Buski10/Offroad-CAD/Import/ToF Bilder/Bild1.jpg

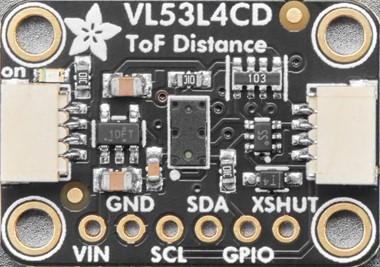
Import/ToF Bilder/Bild1.jpg
