Buski10/Offroad-CAD/Aufsamlung/Arm.SLDPRT

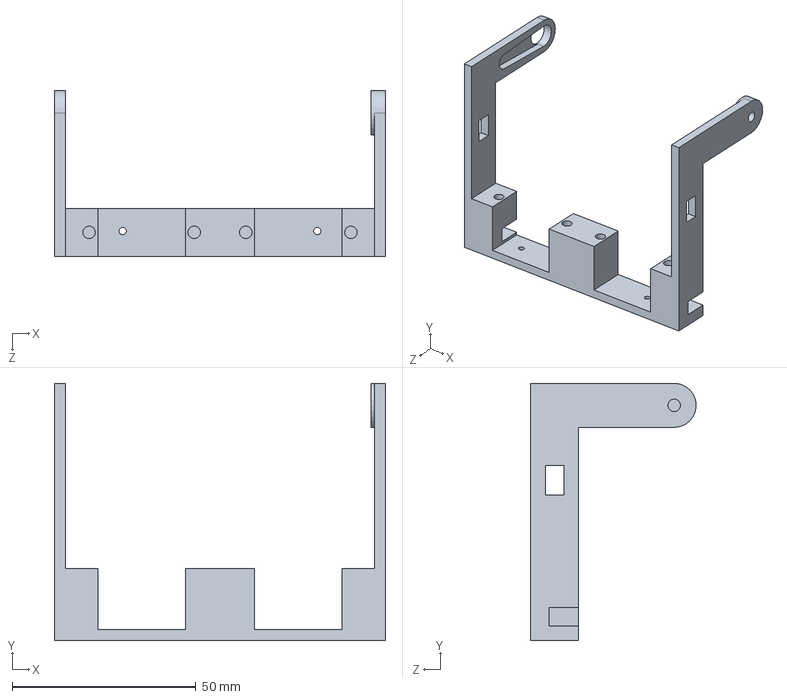
[picture p13: CAD file, 2025-10-28]
Aufsamlung/Arm.SLDPRT
90.0 x 70.0 x 45.0 mm
