Buski10/Offroad-CAD/Fahrgestell/Kamerabox.SLDPRT

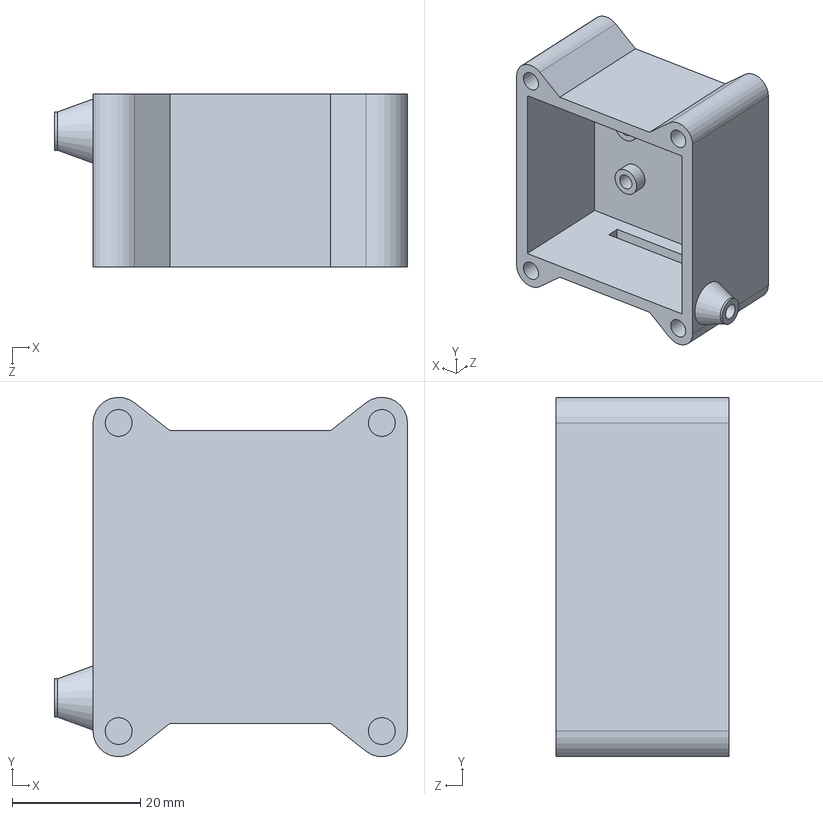
[picture p14: CAD file, 2025-10-28]
Fahrgestell/Kamerabox.SLDPRT
55.0 x 56.0 x 27.0 mm
