Buski10/Offroad-CAD/Import/BNO055/Adafruit_BNO055.SLDPRT

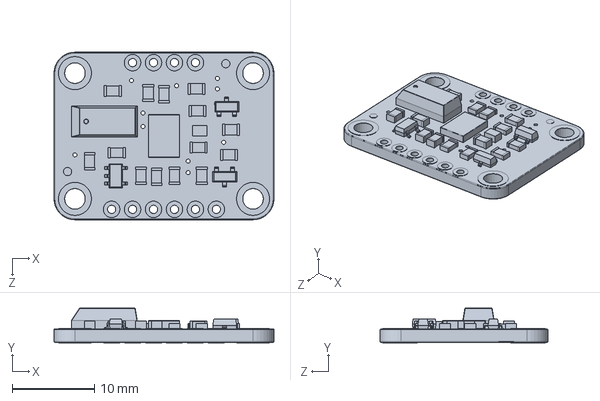
[picture p15: CAD file, 2025-10-28]
Import/BNO055/Adafruit_BNO055.SLDPRT
26.7 x 4.20 x 20.3 mm
