Buski10/Offroad-CAD/Import/ledRing/neopixel.SLDPRT

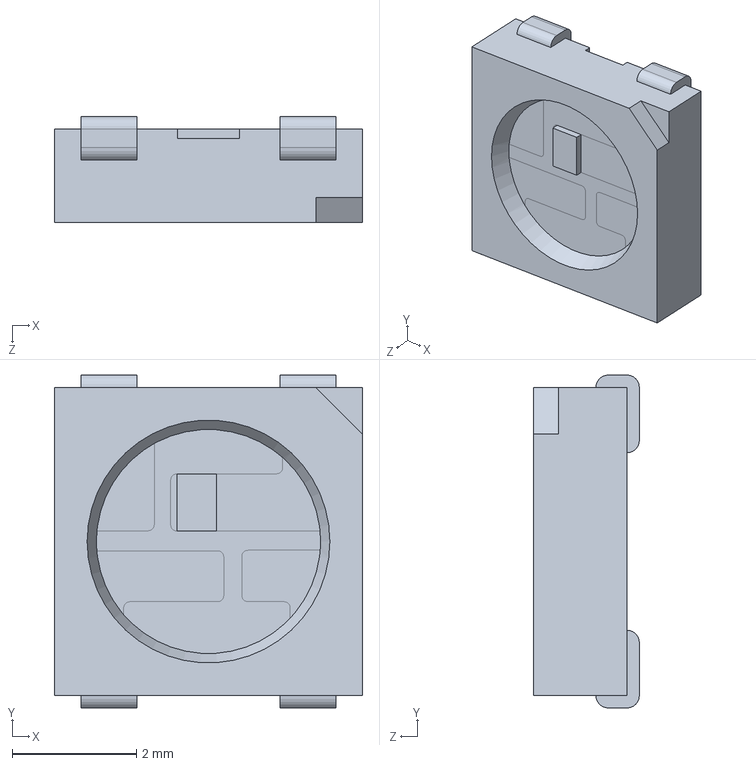
[picture p16: CAD file, 2025-10-28]
Import/ledRing/neopixel.SLDPRT
4.95 x 5.35 x 1.70 mm
