Buski10/Offroad-CAD/Import/Pin Header/pin-90deg.SLDPRT

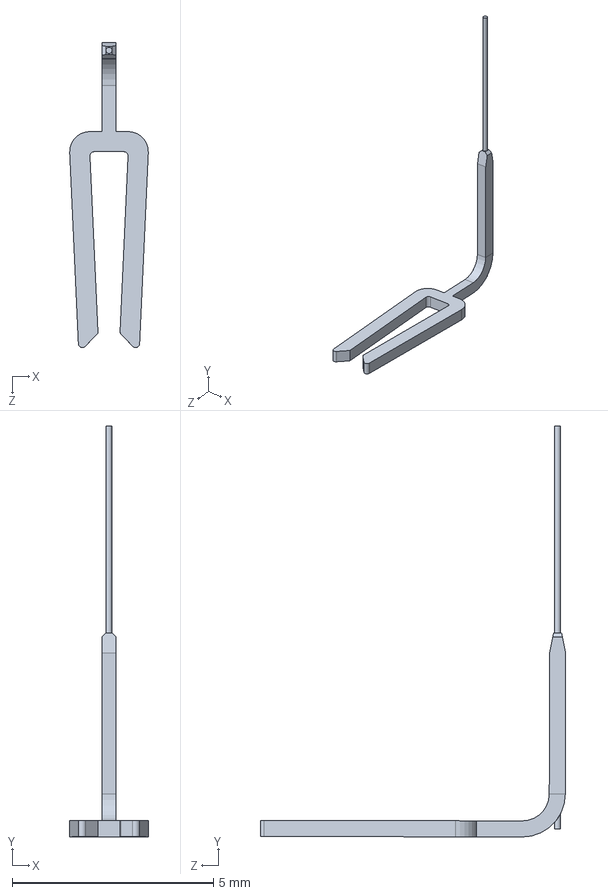
[picture p17: CAD file, 2025-10-28]
Import/Pin Header/pin-90deg.SLDPRT
1.95 x 10.2 x 7.58 mm
