Buski10/Offroad-CAD/Import/rpiCamera/kameraBlickwinkel.SLDPRT

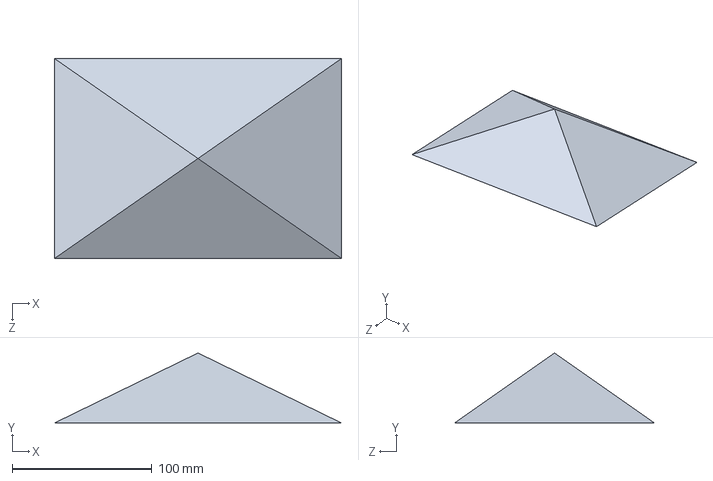
[picture p18: CAD file, 2025-10-28]
Import/rpiCamera/kameraBlickwinkel.SLDPRT
205.0 x 50.0 x 142.8 mm
