Buski10/Offroad-CAD/Import/Schwarz Kugel.SLDPRT

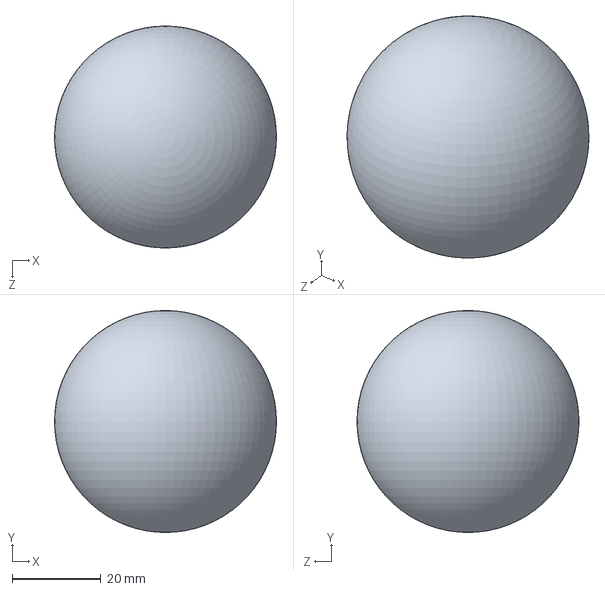
[picture p19: CAD file, 2025-10-28]
Import/Schwarz Kugel.SLDPRT
50.0 x 50.0 x 50.0 mm
