Buski10/Offroad-CAD/Import/Stepper Hat/terminal block_2.SLDPRT

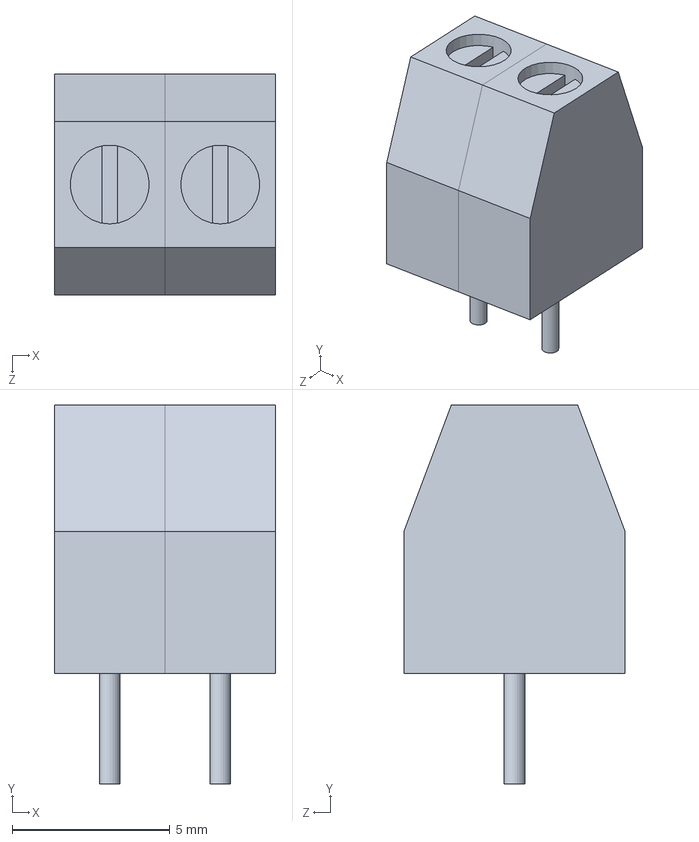
[picture p20: CAD file, 2025-10-28]
Import/Stepper Hat/terminal block_2.SLDPRT
7.00 x 12.0 x 7.00 mm
