Buski10/Offroad-CAD/Motorhalterungen/Achse Motorhalterung.SLDPRT

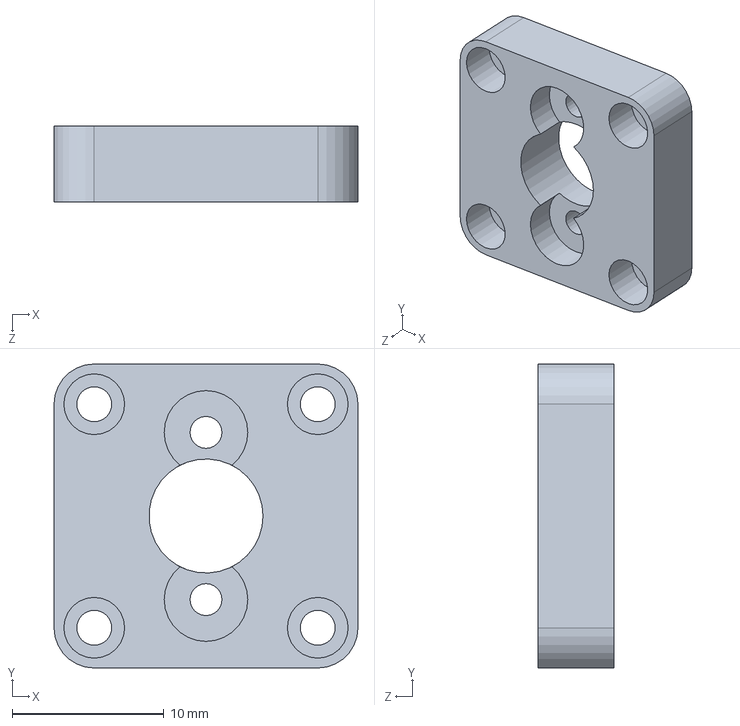
[picture p21: CAD file, 2025-10-28]
Motorhalterungen/Achse Motorhalterung.SLDPRT
20.0 x 20.0 x 5.00 mm
