Buski10/Offroad-CAD/Räder/Radschraube.SLDPRT

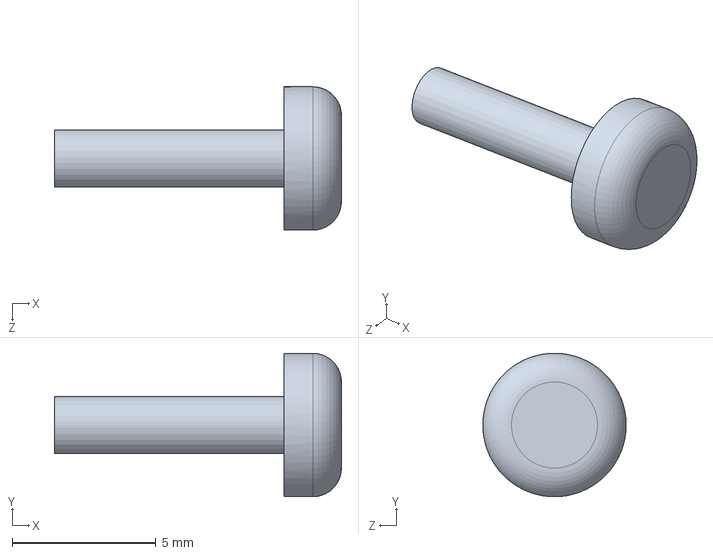
[picture p22: CAD file, 2025-10-28]
Räder/Radschraube.SLDPRT
10.0 x 5.00 x 5.00 mm
