Buski10/Offroad-CAD/Aufsamlung/Greifer.SLDPRT

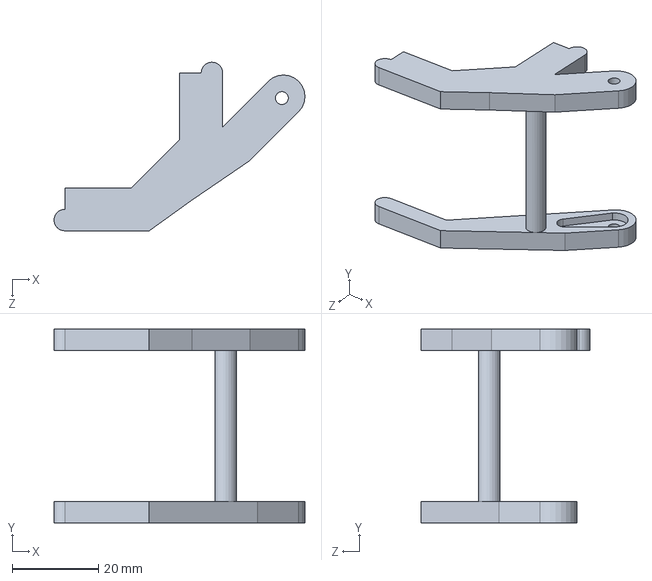
[picture p23: CAD file, 2025-10-28]
Aufsamlung/Greifer.SLDPRT
58.2 x 45.0 x 39.1 mm
