Buski10/Offroad-CAD/Fahrgestell/Grundplatte.SLDPRT

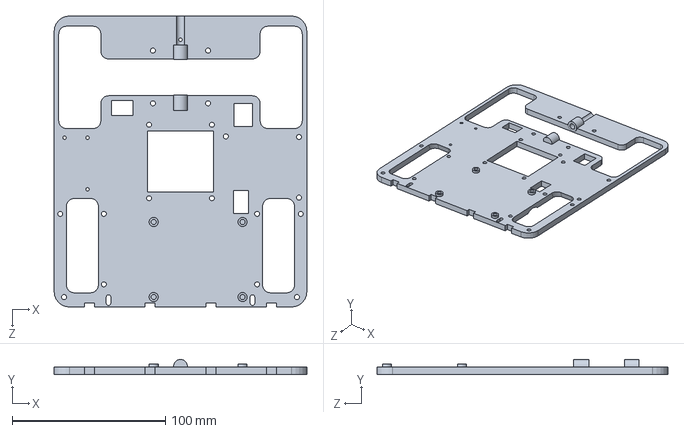
[picture p24: CAD file, 2025-10-28]
Fahrgestell/Grundplatte.SLDPRT
165.0 x 10.0 x 190.0 mm
