Buski10/Offroad-CAD/Import/ledRing/GRM188R60J226MEA0J.SLDPRT

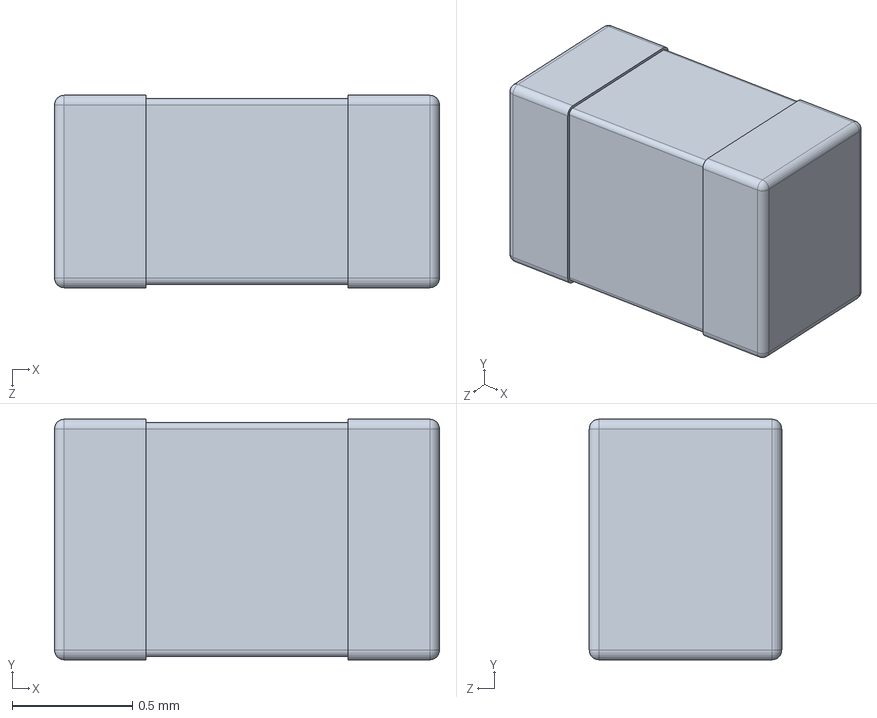
[picture p25: CAD file, 2025-10-28]
Import/ledRing/GRM188R60J226MEA0J.SLDPRT
1.60 x 1.00 x 0.8 mm
