Buski10/Offroad-CAD/Import/Micro SD Card.SLDPRT

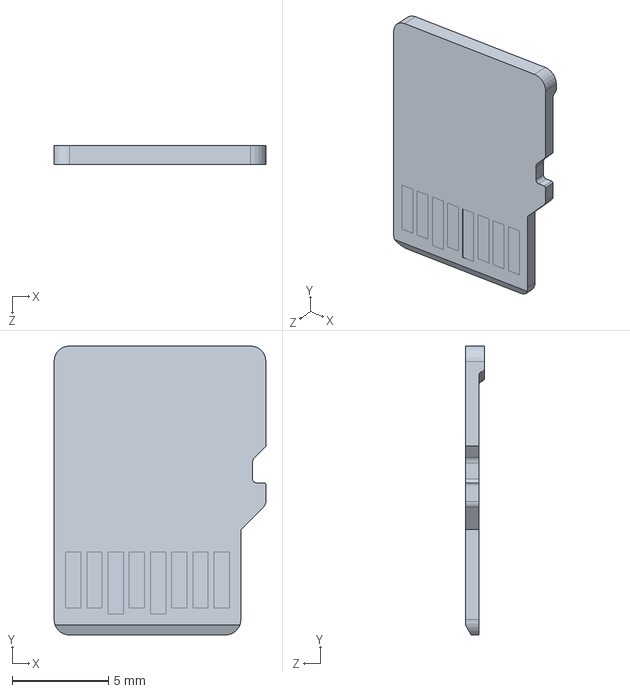
[picture p26: CAD file, 2025-10-28]
Import/Micro SD Card.SLDPRT
11.0 x 15.0 x 1.00 mm
