Buski10/Offroad-CAD/Import/Motor/1524T_SR.SLDPRT

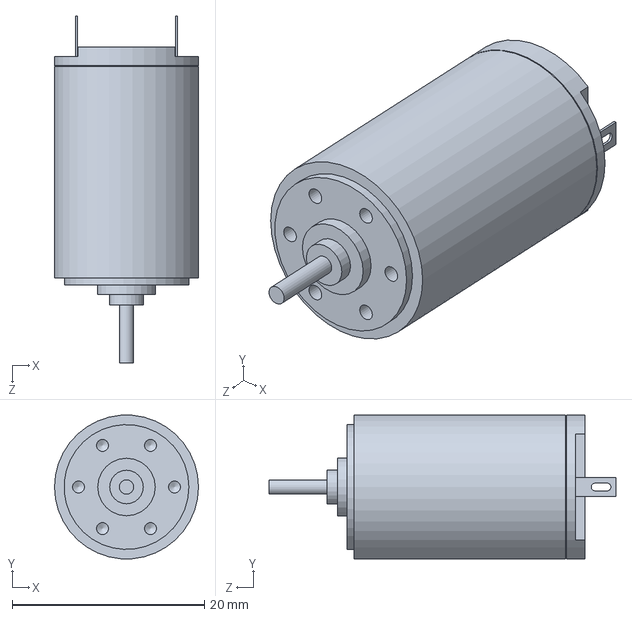
[picture p27: CAD file, 2025-10-28]
Import/Motor/1524T_SR.SLDPRT
15.0 x 14.9 x 36.1 mm
