Buski10/Offroad-CAD/Import/Pin Header/1x4 Male Pin Header Angle.SLDPRT

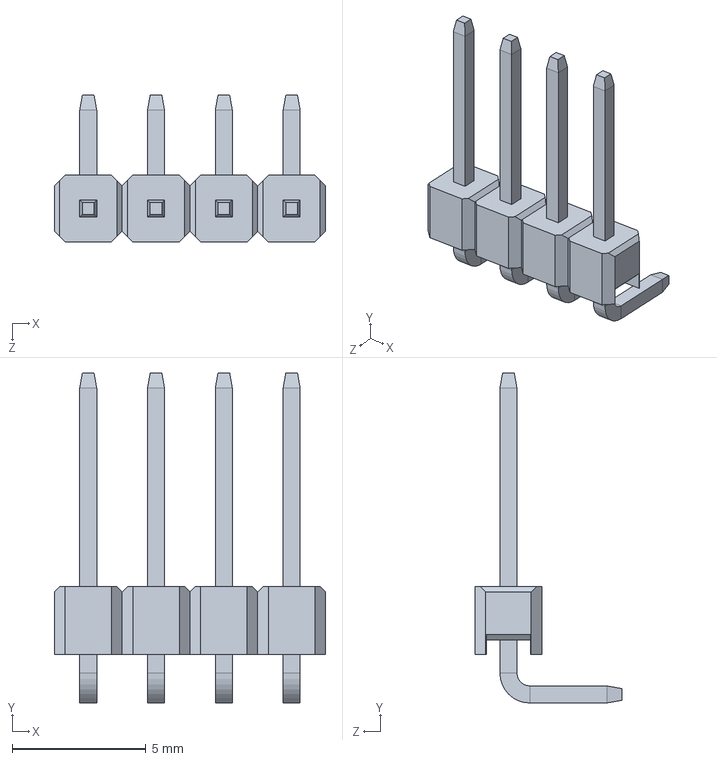
[picture p28: CAD file, 2025-10-28]
Import/Pin Header/1x4 Male Pin Header Angle.SLDPRT
10.2 x 12.4 x 5.50 mm
