Buski10/Offroad-CAD/Import/Stepper Hat/terminal block_3.SLDPRT

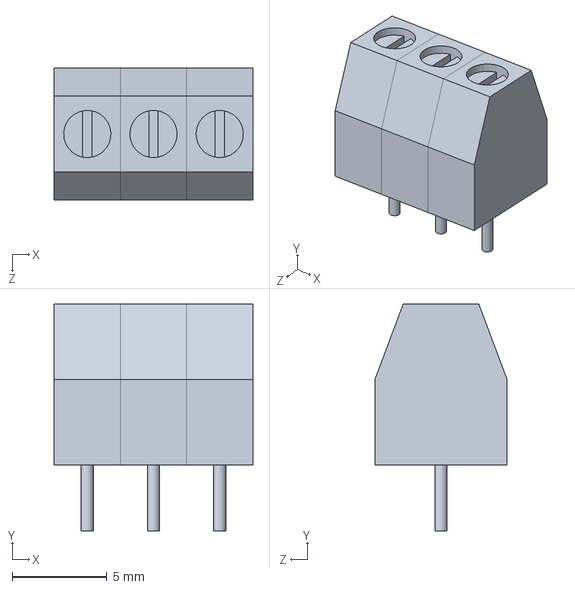
[picture p29: CAD file, 2025-10-28]
Import/Stepper Hat/terminal block_3.SLDPRT
10.5 x 12.0 x 7.00 mm
