Buski10/Offroad-CAD/Lipo Begrenzer.SLDPRT

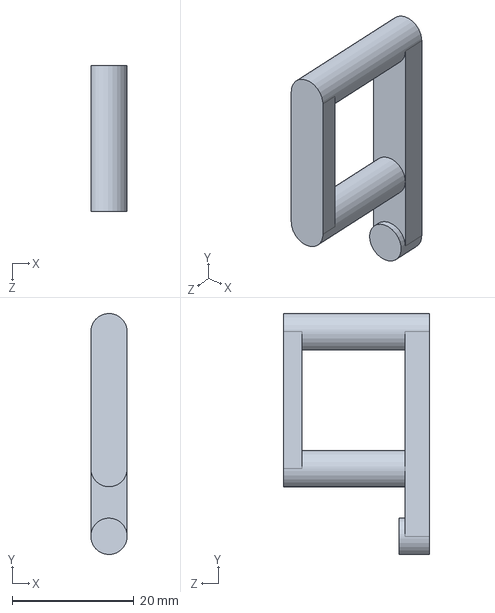
[picture p30: CAD file, 2025-10-28]
Lipo Begrenzer.SLDPRT
6.00 x 39.6 x 24.0 mm
