Buski10/Offroad-CAD/Motorhalterungen/Achse Motorhalterung rechts.SLDPRT

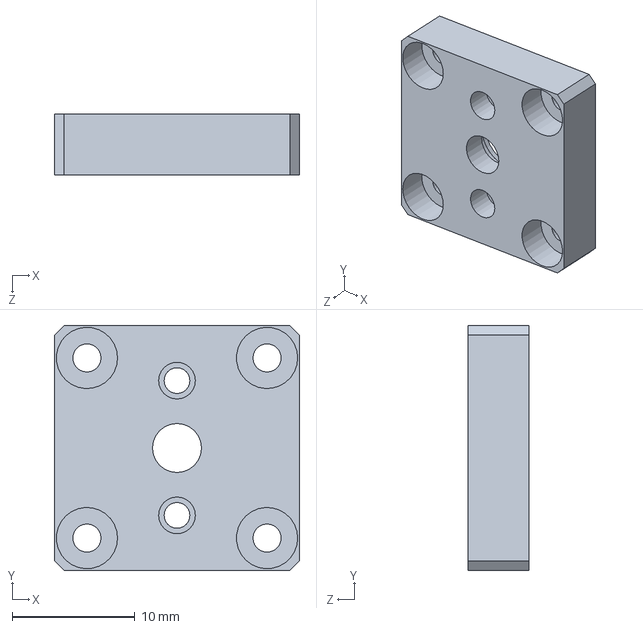
[picture p31: CAD file, 2025-10-28]
Motorhalterungen/Achse Motorhalterung rechts.SLDPRT
20.0 x 20.0 x 5.00 mm
