Buski10/Offroad-CAD/Rutsche/Kugelblocker.SLDPRT

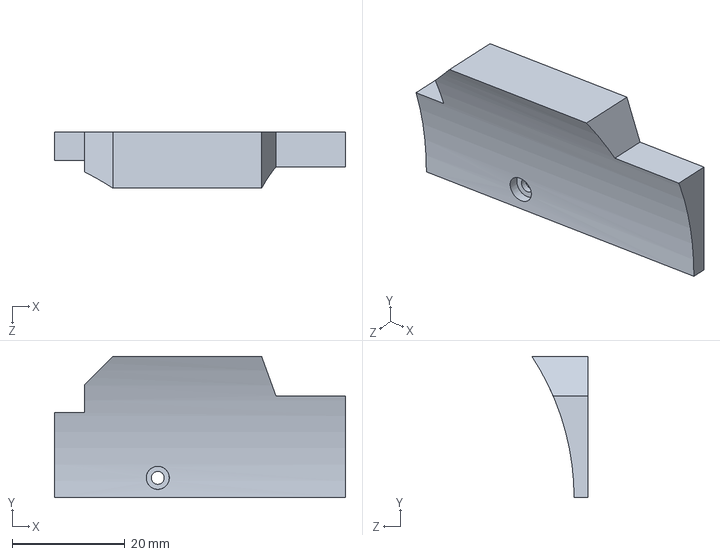
[picture p32: CAD file, 2025-10-28]
Rutsche/Kugelblocker.SLDPRT
51.7 x 25.1 x 10.0 mm
