Buski10/Offroad-CAD/Aufsamlung/SpiegelnGreifer.SLDPRT

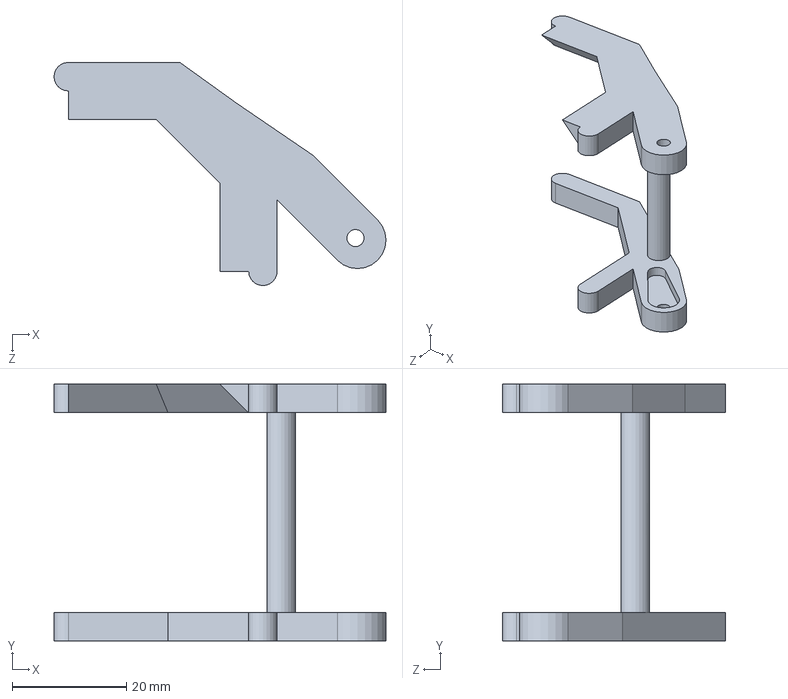
[picture p33: CAD file, 2025-10-28]
Aufsamlung/SpiegelnGreifer.SLDPRT
58.2 x 45.0 x 39.1 mm
