Buski10/Offroad-CAD/Import/7.5V, 3A step down.SLDPRT

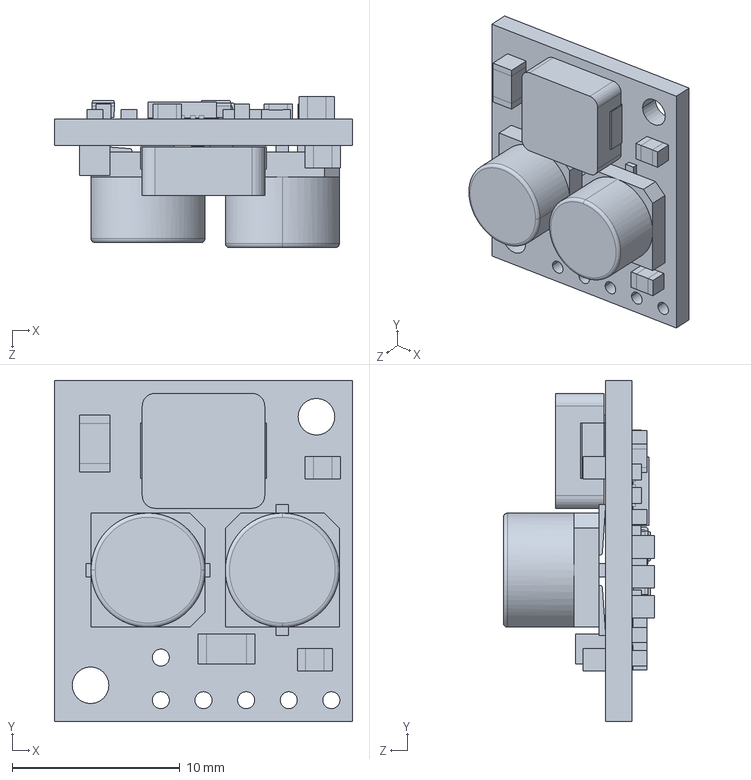
[picture p34: CAD file, 2025-10-28]
Import/7.5V, 3A step down.SLDPRT
17.8 x 20.3 x 9.02 mm
