Buski10/Offroad-CAD/Import/Motor/15A_3stage.SLDPRT

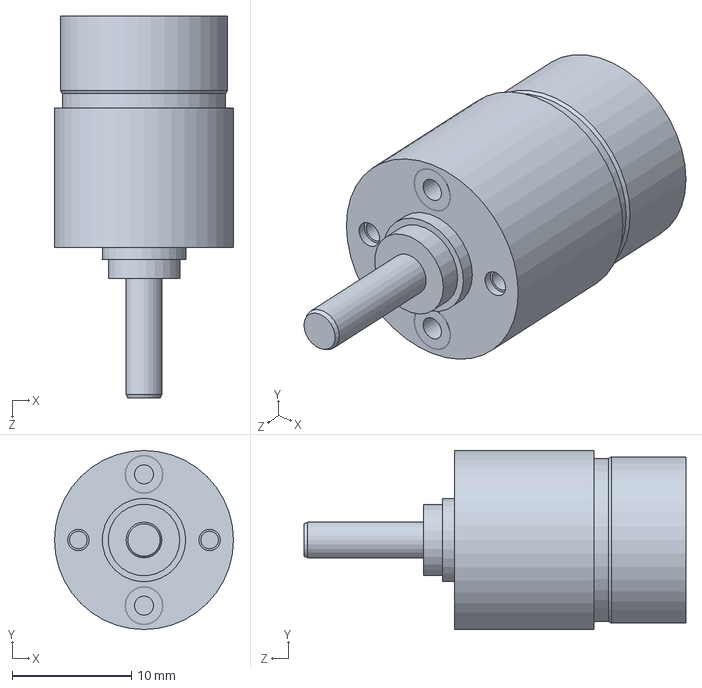
[picture p35: CAD file, 2025-10-28]
Import/Motor/15A_3stage.SLDPRT
15.0 x 15.0 x 32.0 mm
