Buski10/Offroad-CAD/Import/Pin Header/frame_H254.sldprt

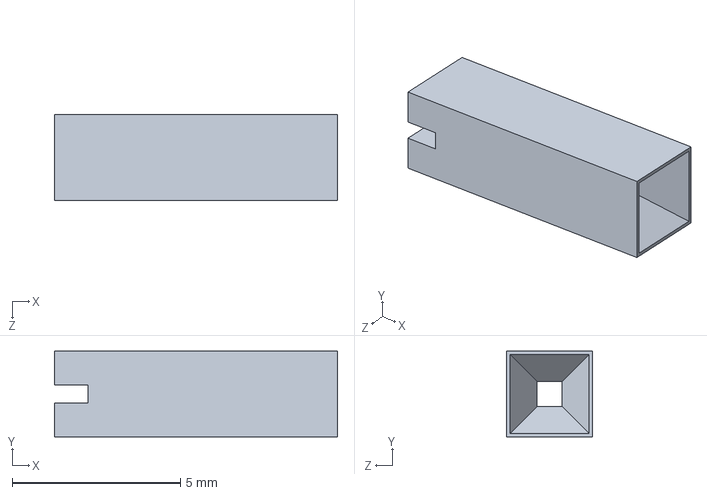
[picture p36: CAD file, 2025-10-28]
Import/Pin Header/frame_H254.sldprt
8.40 x 2.54 x 2.54 mm
