Buski10/Offroad-CAD/Import/RPi Active Cooler/Spring.SLDPRT

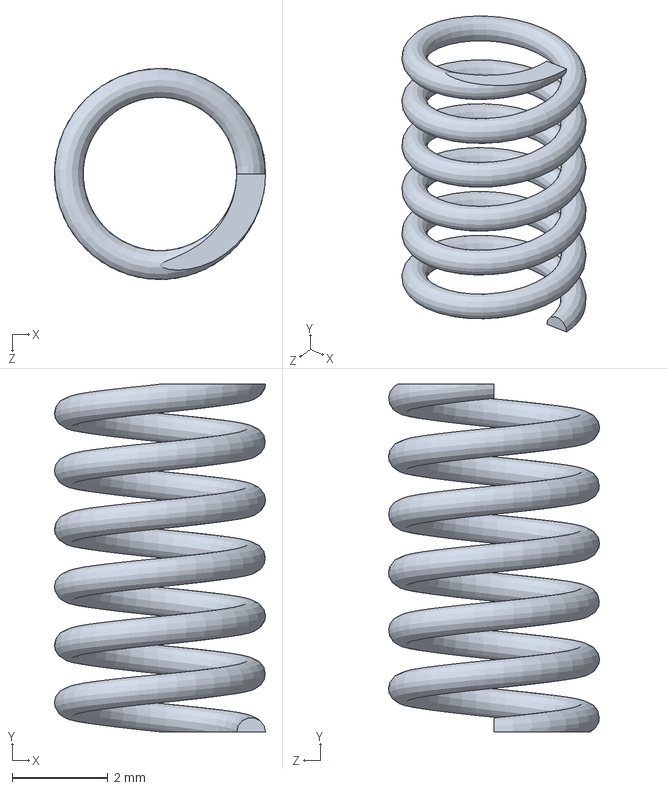
[picture p37: CAD file, 2025-10-28]
Import/RPi Active Cooler/Spring.SLDPRT
4.40 x 7.25 x 4.40 mm
