Buski10/Offroad-CAD/Import/rpiCamera/rpiCameraM.SLDPRT

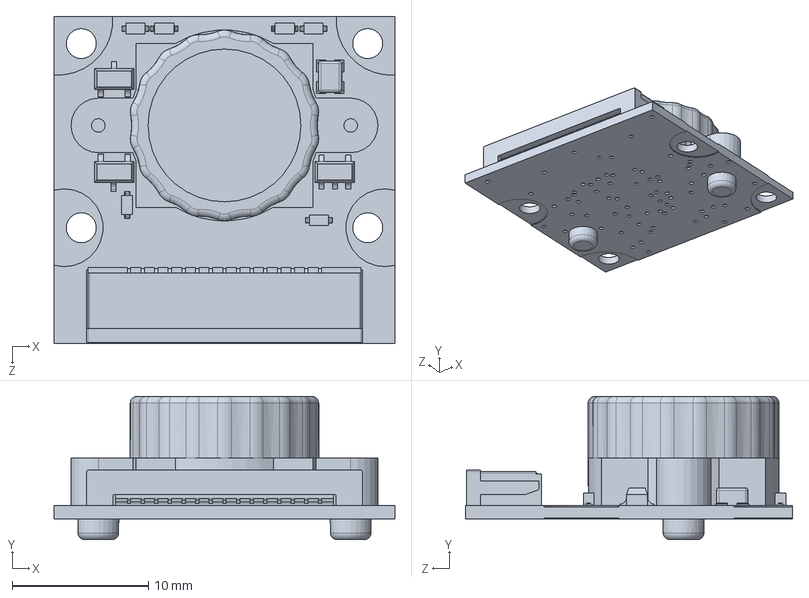
[picture p38: CAD file, 2025-10-28]
Import/rpiCamera/rpiCameraM.SLDPRT
25.0 x 10.5 x 24.0 mm
