Buski10/Offroad-CAD/Import/Stepper Hat/AdafruitStepperHat.SLDPRT

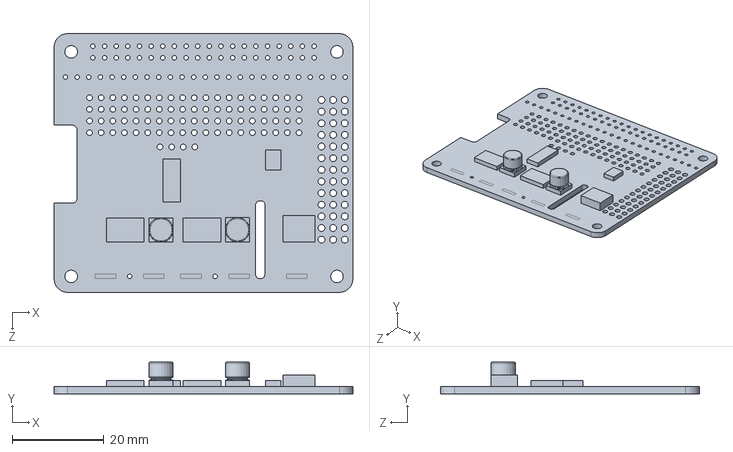
[picture p39: CAD file, 2025-10-28]
Import/Stepper Hat/AdafruitStepperHat.SLDPRT
65.2 x 6.90 x 56.5 mm
