Buski10/Offroad-CAD/Rutsche/Rutsche.SLDPRT

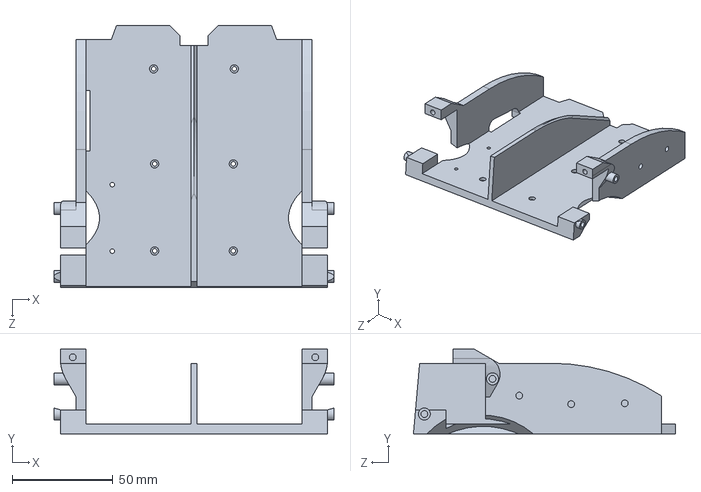
[picture p40: CAD file, 2025-10-28]
Rutsche/Rutsche.SLDPRT
138.9 x 42.0 x 130.0 mm
