Buski10/Offroad-CAD/Räder/Silikon Rad Guss.SLDPRT

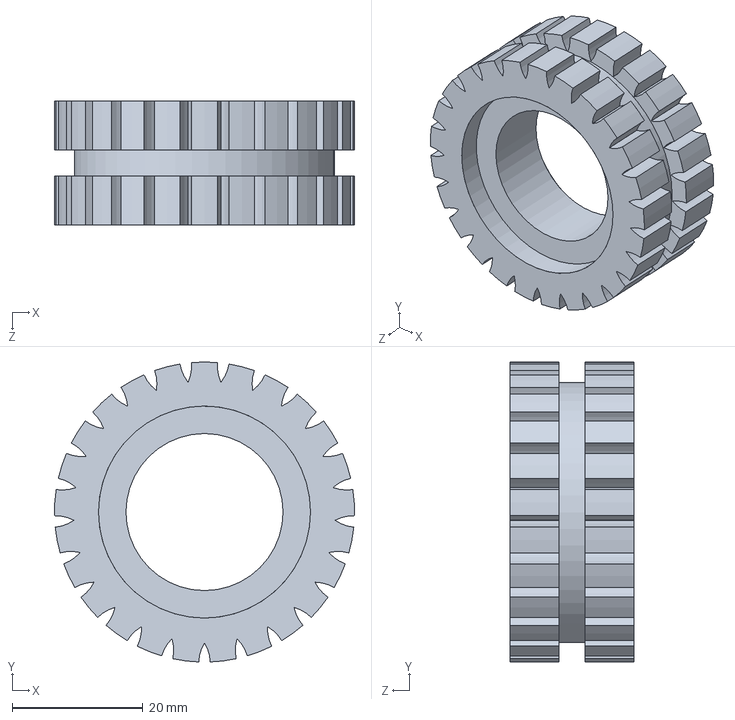
[picture p41: CAD file, 2025-10-28]
Räder/Silikon Rad Guss.SLDPRT
45.8 x 45.8 x 19.0 mm
