Buski10/Offroad-CAD/Tasterstange.SLDPRT

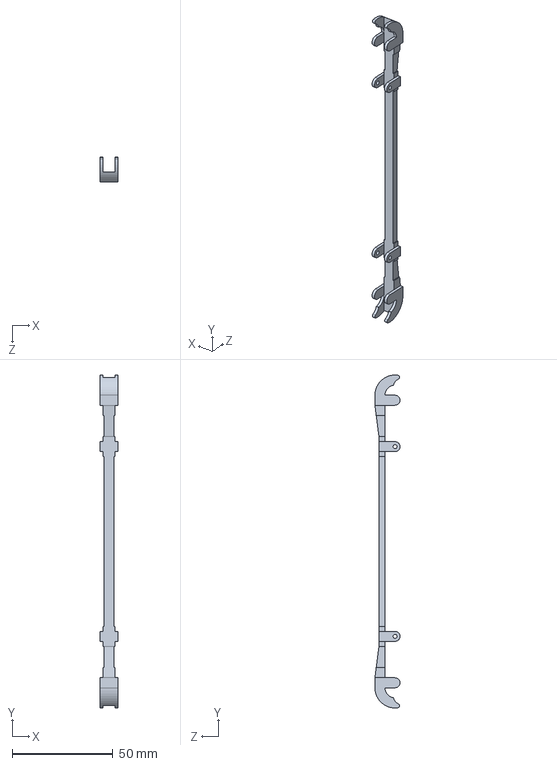
[picture p42: CAD file, 2025-10-28]
Tasterstange.SLDPRT
9.00 x 165.0 x 12.5 mm
