Buski10/Offroad-CAD/Import/Motor/15A_flange_a.stp.SLDPRT

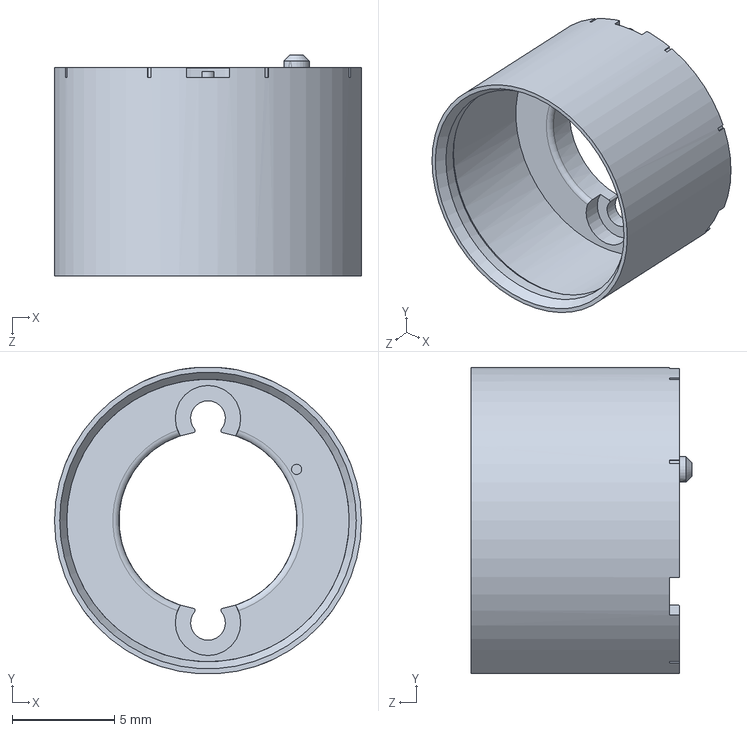
[picture p43: CAD file, 2025-10-28]
Import/Motor/15A_flange_a.stp.SLDPRT
15.0 x 15.0 x 10.8 mm
