Buski10/Offroad-CAD/Import/RPi Active Cooler/RotorBlades.SLDPRT

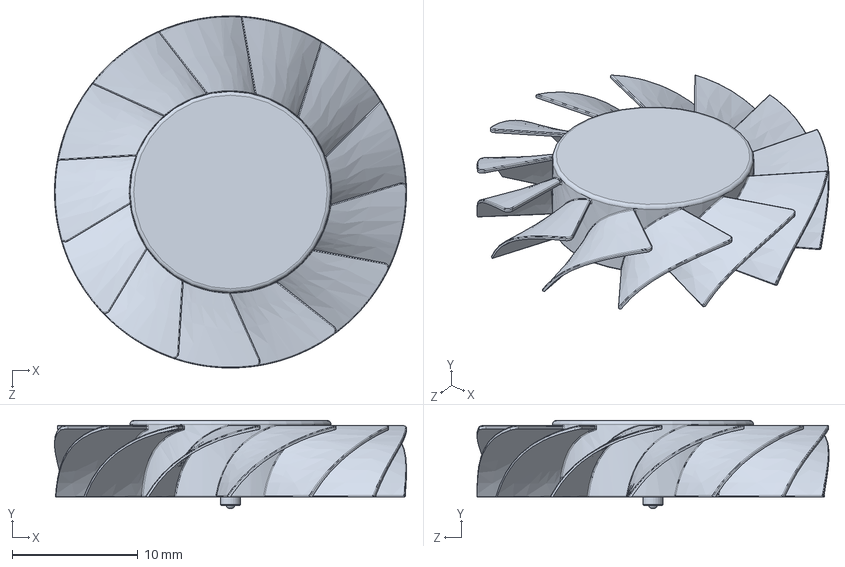
[picture p44: CAD file, 2025-10-28]
Import/RPi Active Cooler/RotorBlades.SLDPRT
28.0 x 7.00 x 28.0 mm
