Buski10/Offroad-CAD/Import/rpiCamera/rpiCameraM_lens.SLDPRT

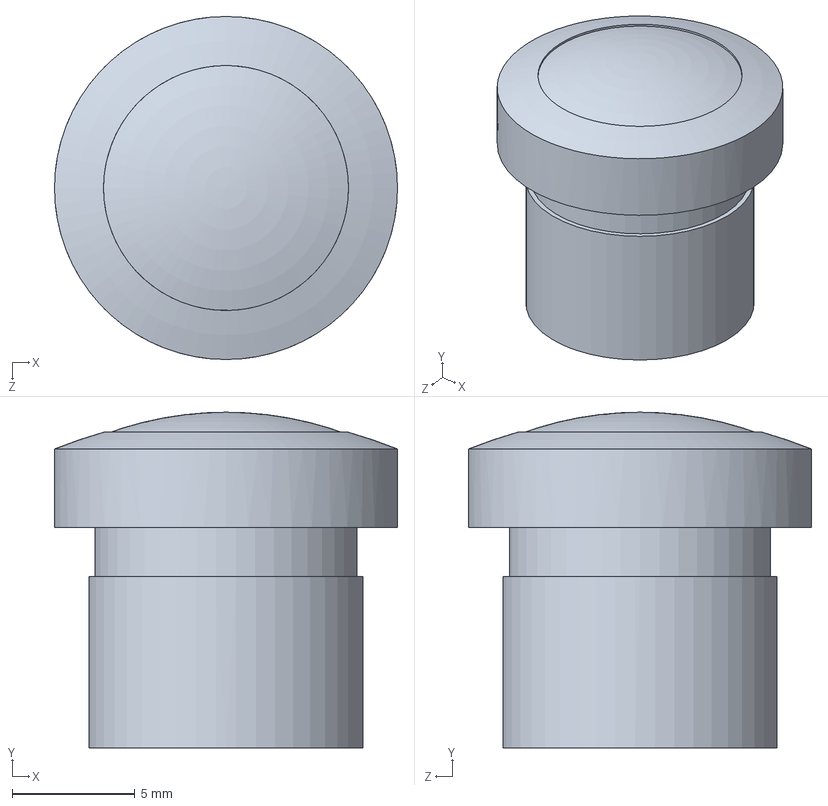
[picture p45: CAD file, 2025-10-28]
Import/rpiCamera/rpiCameraM_lens.SLDPRT
14.0 x 13.7 x 14.0 mm
