Buski10/Offroad-CAD/Import/Servo S90/MicroServo-SG90.SLDPRT

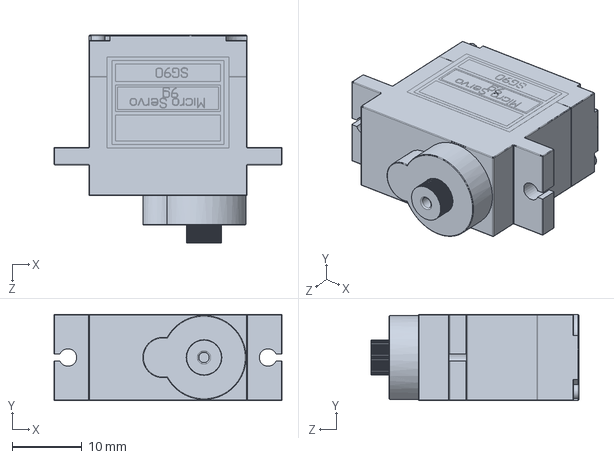
[picture p46: CAD file, 2025-10-28]
Import/Servo S90/MicroServo-SG90.SLDPRT
32.6 x 12.4 x 29.8 mm
