Buski10/Offroad-CAD/Import/Stepper Hat/40pin.SLDPRT

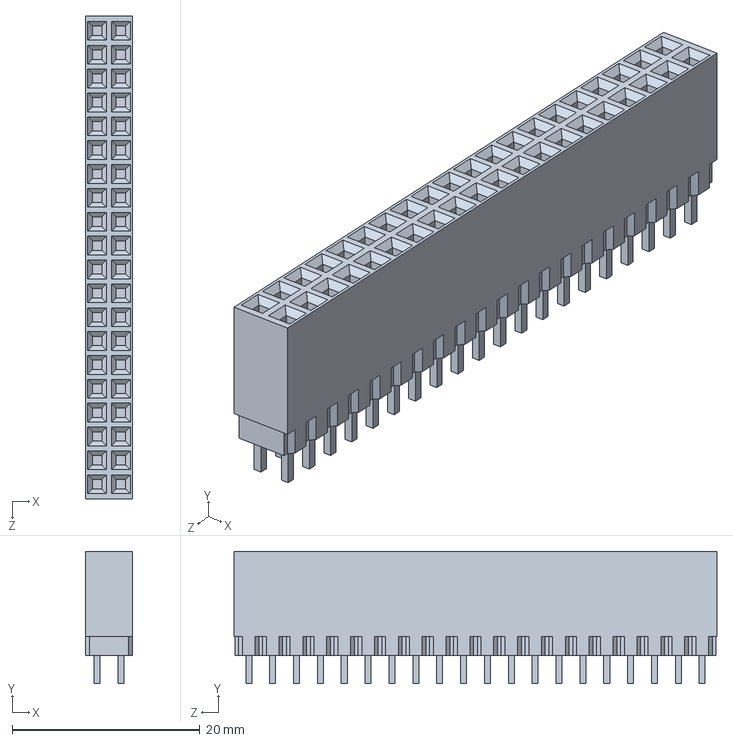
[picture p47: CAD file, 2025-10-28]
Import/Stepper Hat/40pin.SLDPRT
5.00 x 14.1 x 51.4 mm
