Buski10/Offroad-CAD/Import/usb-c-connector-board.SLDPRT

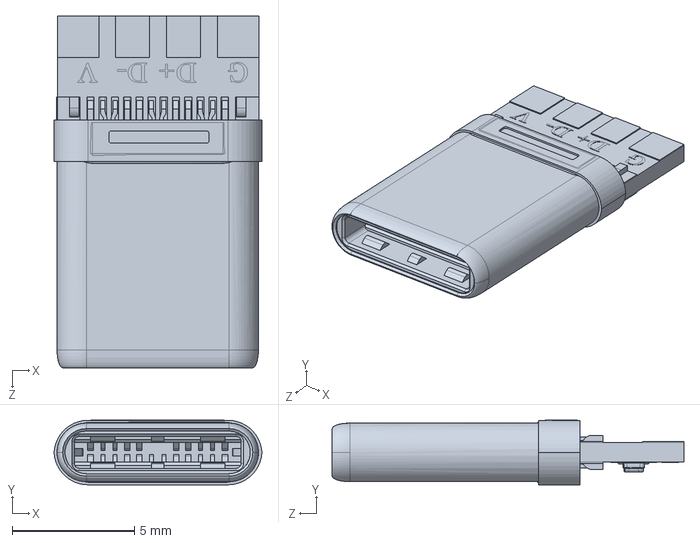
[picture p48: CAD file, 2025-10-28]
Import/usb-c-connector-board.SLDPRT
8.52 x 2.65 x 14.4 mm
