Buski10/Offroad-CAD/Rutsche/Schranke.SLDPRT

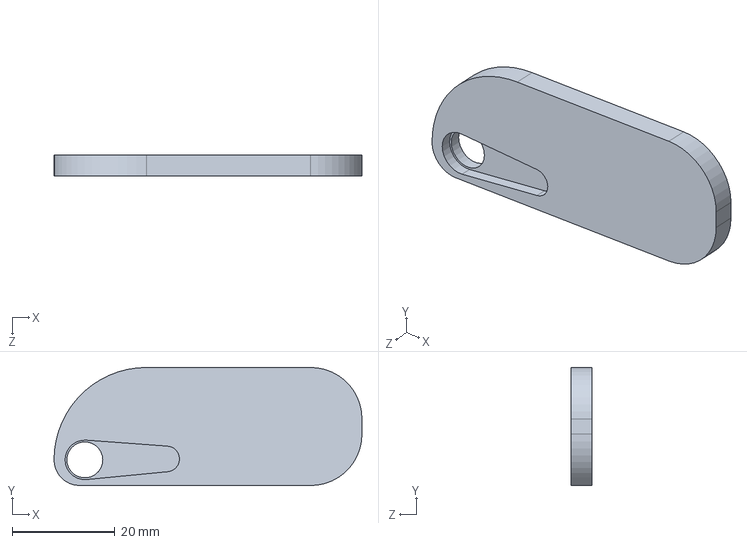
[picture p49: CAD file, 2025-10-28]
Rutsche/Schranke.SLDPRT
60.0 x 23.0 x 4.00 mm
