Buski10/Offroad-CAD/Räder/Silikon Rad.SLDPRT

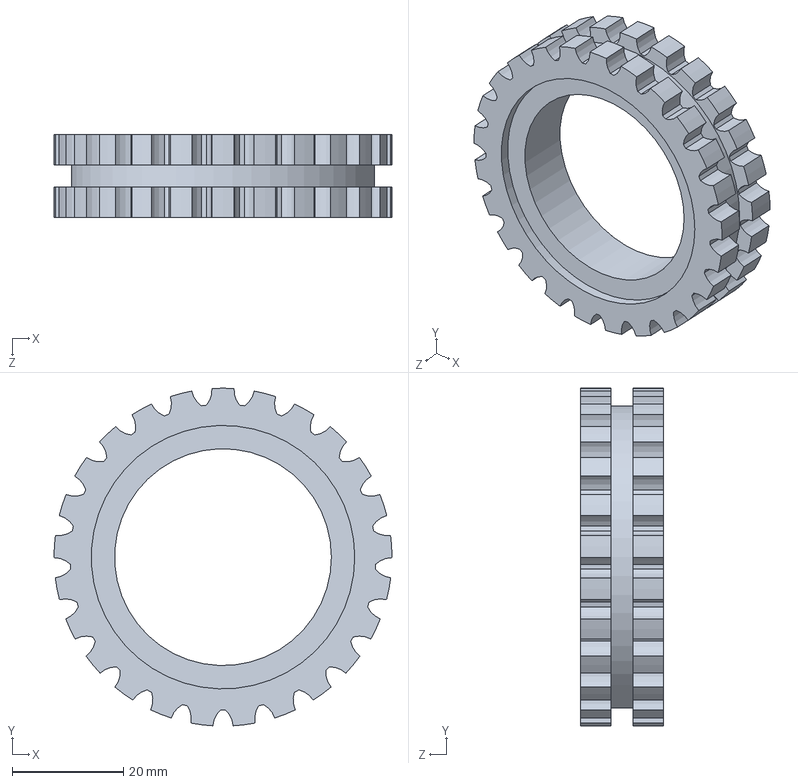
[picture p50: CAD file, 2025-10-28]
Räder/Silikon Rad.SLDPRT
60.8 x 60.7 x 15.0 mm
