Buski10/Offroad-CAD/ToF Vorne Links V2.0.SLDPRT

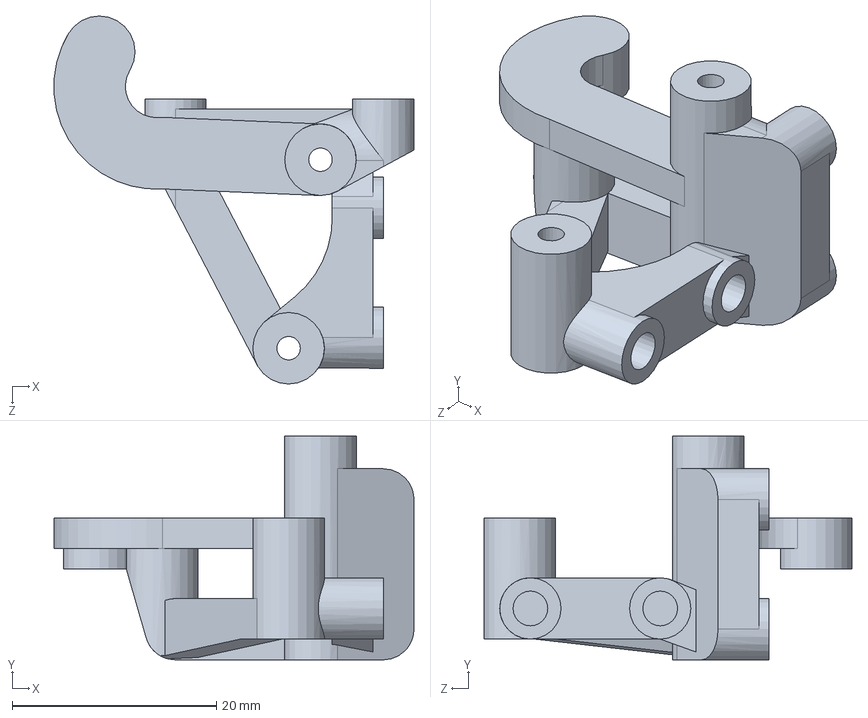
[picture p51: CAD file, 2025-10-28]
ToF Vorne Links V2.0.SLDPRT
35.2 x 21.9 x 36.0 mm
