Buski10/Offroad-CAD/Rutsche/Rutschehalterung.SLDPRT

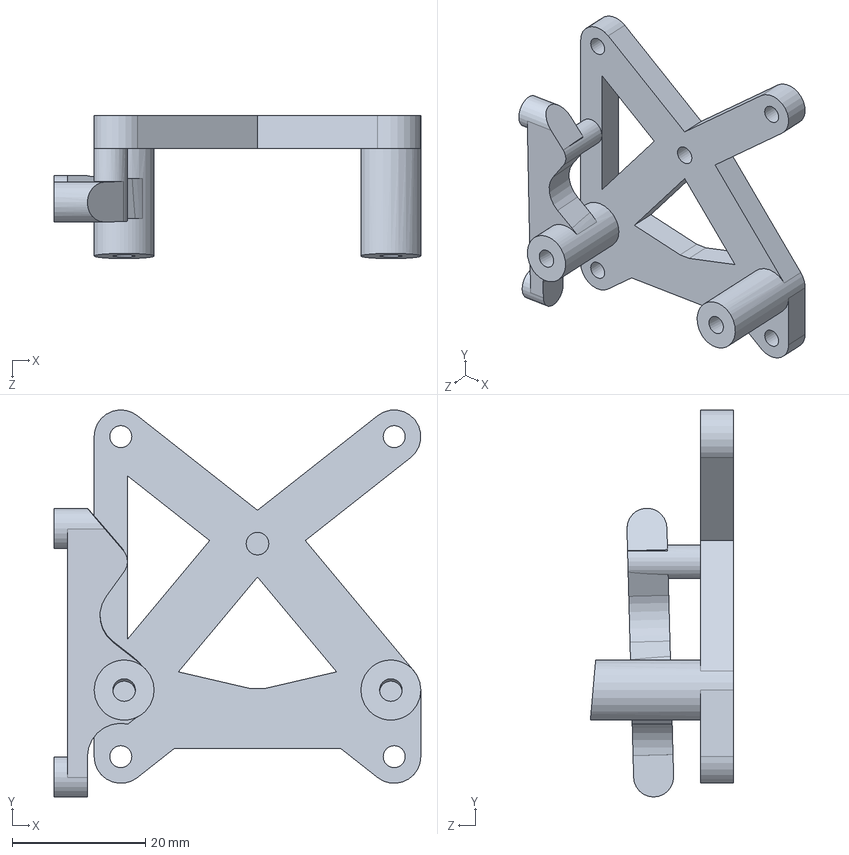
[picture p52: CAD file, 2025-10-28]
Rutsche/Rutschehalterung.SLDPRT
55.0 x 58.0 x 21.5 mm
