Buski10/Offroad-CAD/Räder/Felge.SLDPRT

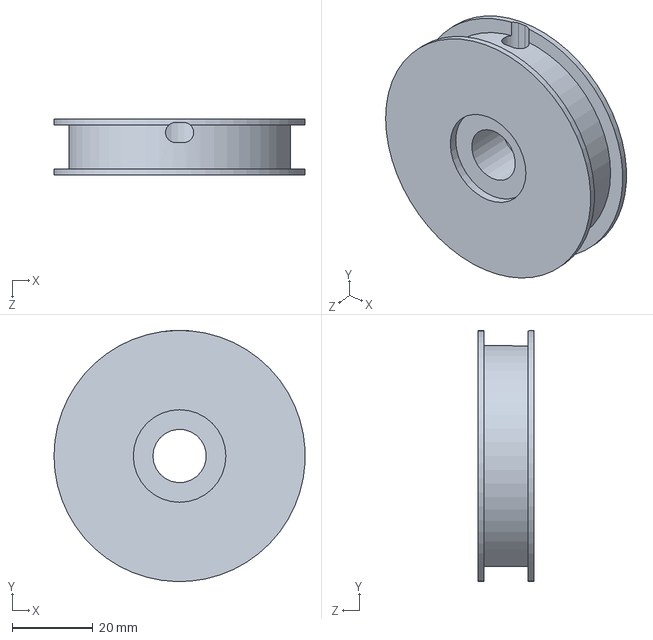
[picture p53: CAD file, 2025-10-28]
Räder/Felge.SLDPRT
62.3 x 62.4 x 14.0 mm
