Buski10/Offroad-CAD/Vordere Kamerahalterung.SLDPRT

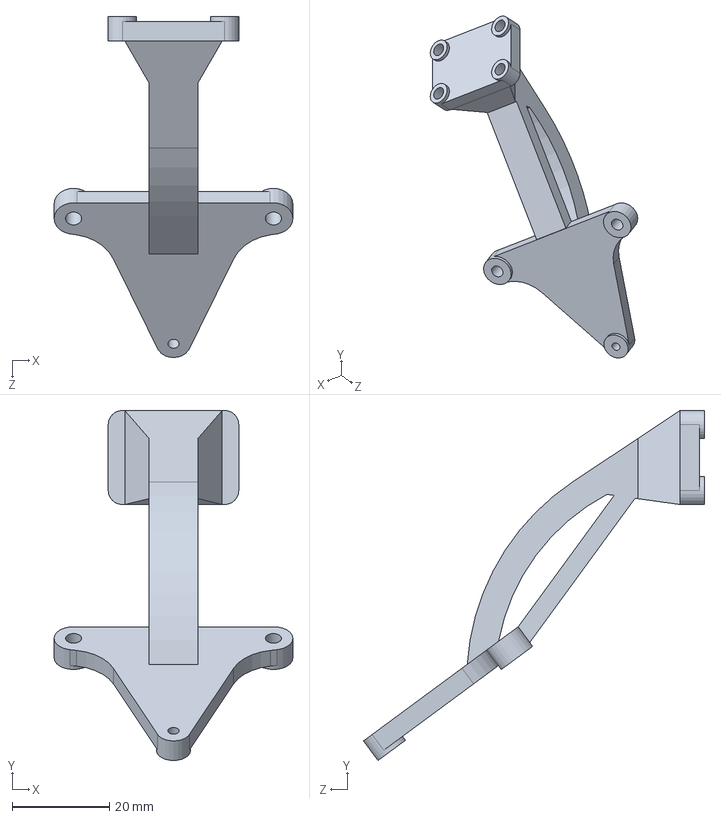
[picture p54: CAD file, 2025-10-28]
Vordere Kamerahalterung.SLDPRT
49.0 x 71.8 x 70.0 mm
