Buski10/Offroad-CAD/Import/RPi Active Cooler/Heatsink-fan-base_RPi5.SLDPRT

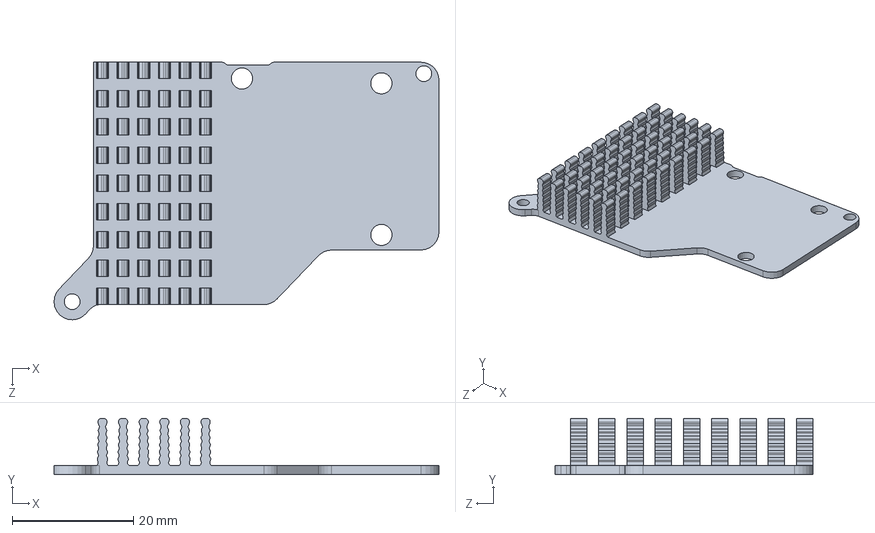
[picture p55: CAD file, 2025-10-28]
Import/RPi Active Cooler/Heatsink-fan-base_RPi5.SLDPRT
63.5 x 9.30 x 42.5 mm
