Buski10/Offroad-CAD/Kompliziertes Teil.SLDPRT

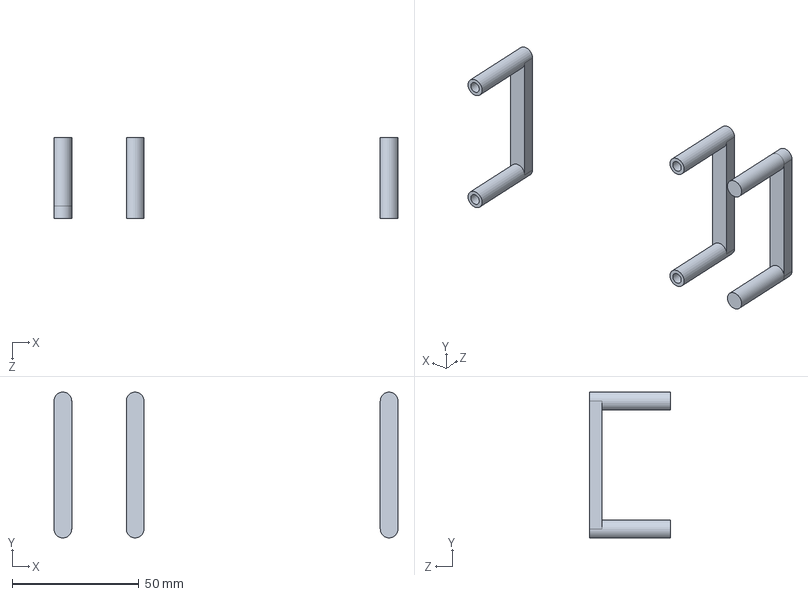
[picture p56: CAD file, 2025-10-28]
Kompliziertes Teil.SLDPRT
135.6 x 57.5 x 32.0 mm
