Buski10/Offroad-CAD/Motorhalterungen/Motorhalterung vorne.SLDPRT

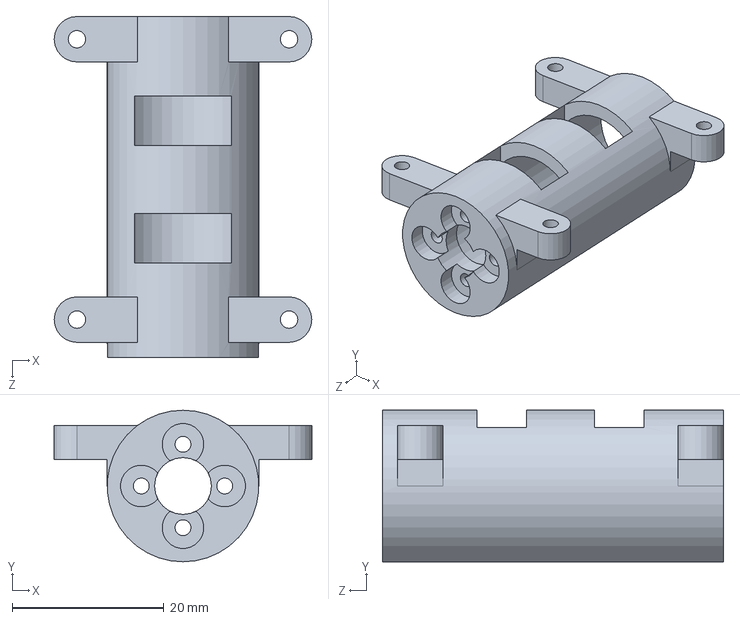
[picture p57: CAD file, 2025-10-28]
Motorhalterungen/Motorhalterung vorne.SLDPRT
34.0 x 20.0 x 45.0 mm
