Buski10/Offroad-CAD/Hintere ToF Halterung.SLDPRT

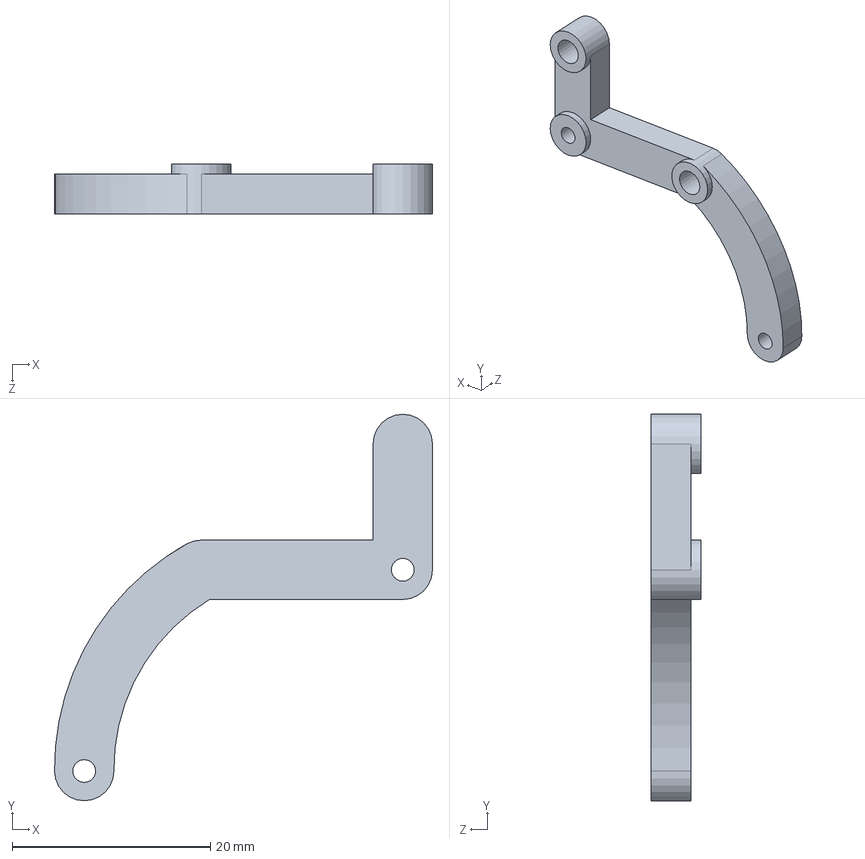
[picture p58: CAD file, 2025-10-28]
Hintere ToF Halterung.SLDPRT
38.2 x 39.0 x 5.00 mm
