Buski10/Offroad-CAD/Import/RPi Active Cooler/MotorHouse.SLDPRT

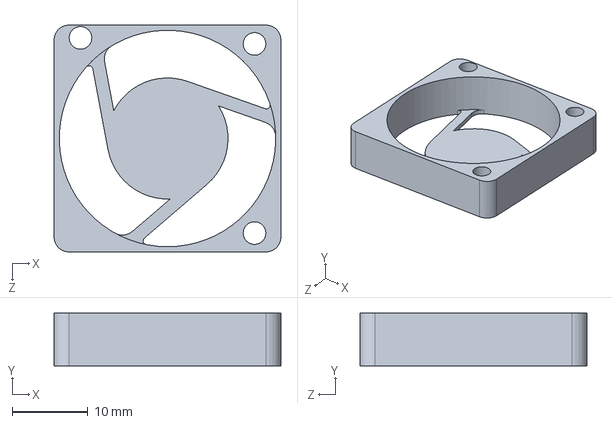
[picture p59: CAD file, 2025-10-28]
Import/RPi Active Cooler/MotorHouse.SLDPRT
30.0 x 7.00 x 30.0 mm
