Buski10/Offroad-CAD/Räder/Felgen Adapter.SLDPRT

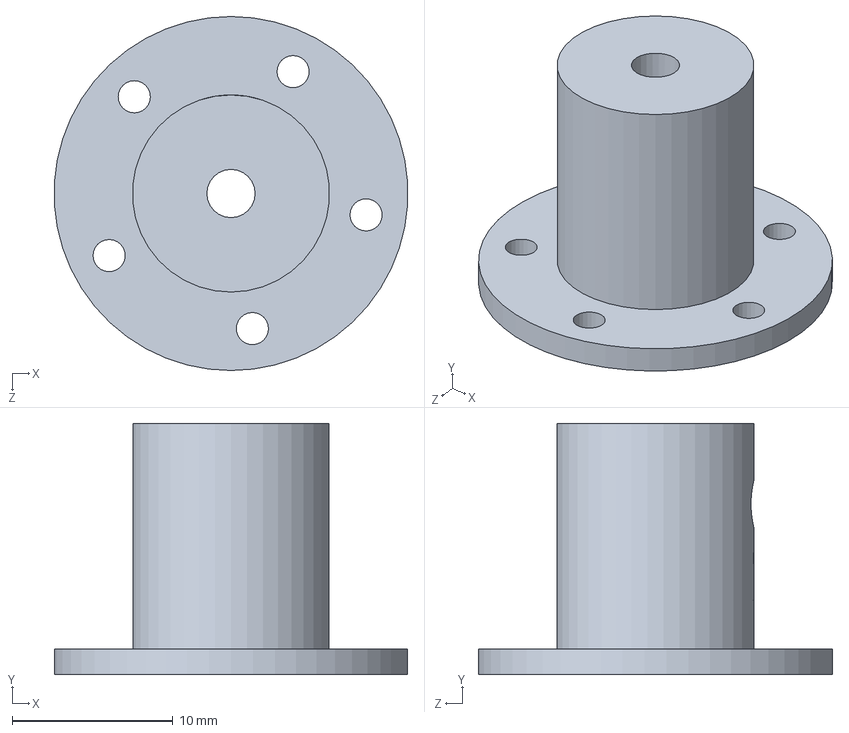
[picture p60: CAD file, 2025-10-28]
Räder/Felgen Adapter.SLDPRT
22.0 x 15.6 x 22.0 mm
