Buski10/Offroad-CAD/Greifer Servo Halterung.SLDPRT

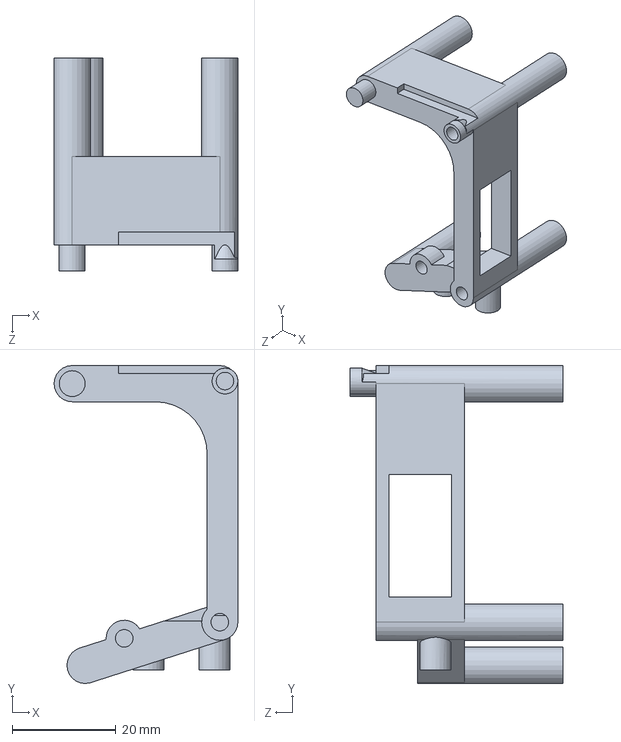
[picture p61: CAD file, 2025-10-28]
Greifer Servo Halterung.SLDPRT
35.5 x 61.4 x 41.0 mm
