Buski10/Offroad-CAD/Import/KST_DS215MG.SLDPRT

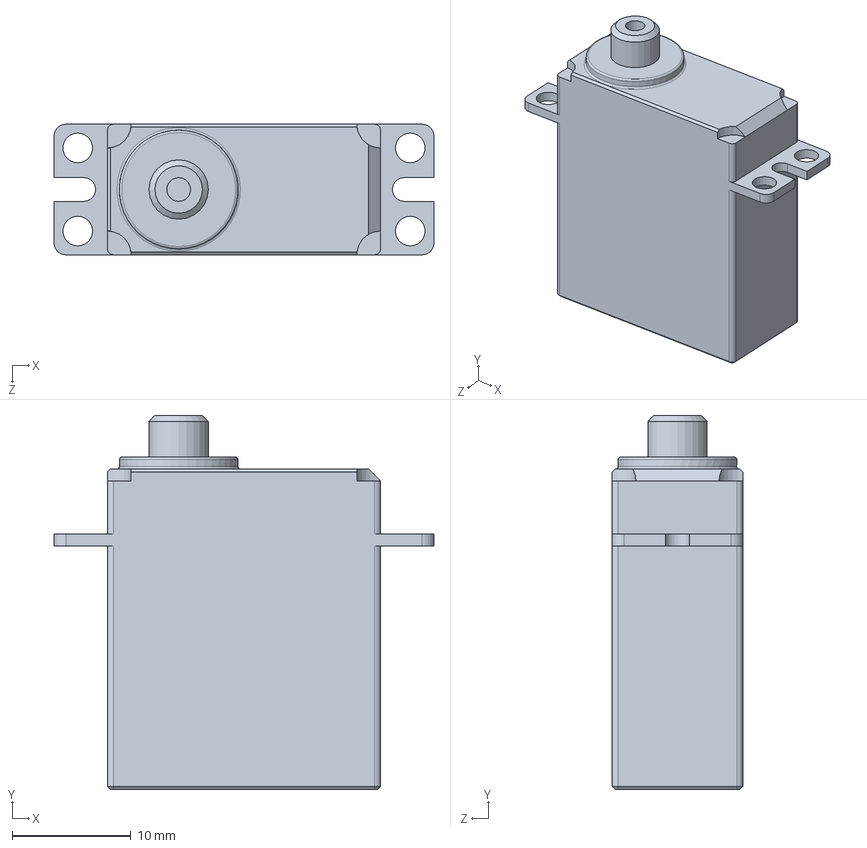
[picture p62: CAD file, 2025-10-28]
Import/KST_DS215MG.SLDPRT
32.0 x 31.5 x 11.0 mm
