Buski10/Offroad-CAD/Räder/Gussform.SLDPRT

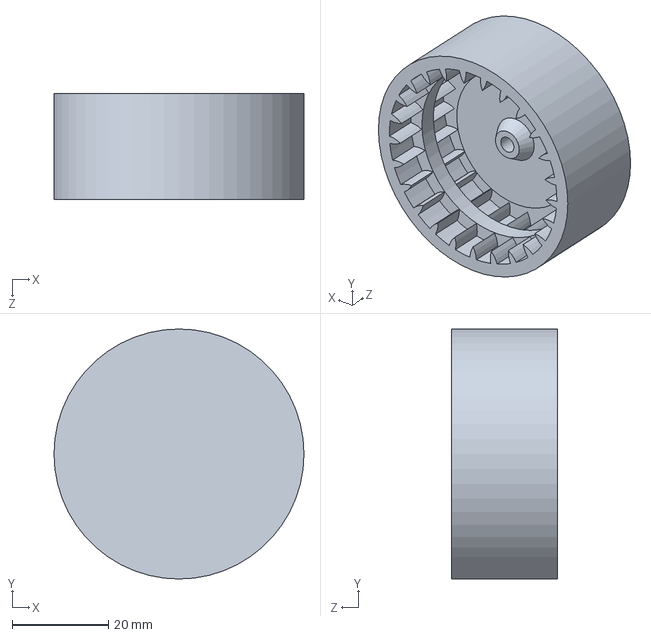
[picture p63: CAD file, 2025-10-28]
Räder/Gussform.SLDPRT
51.9 x 51.9 x 22.0 mm
