Buski10/Offroad-CAD/Import/RPi Active Cooler/fan cover.SLDPRT

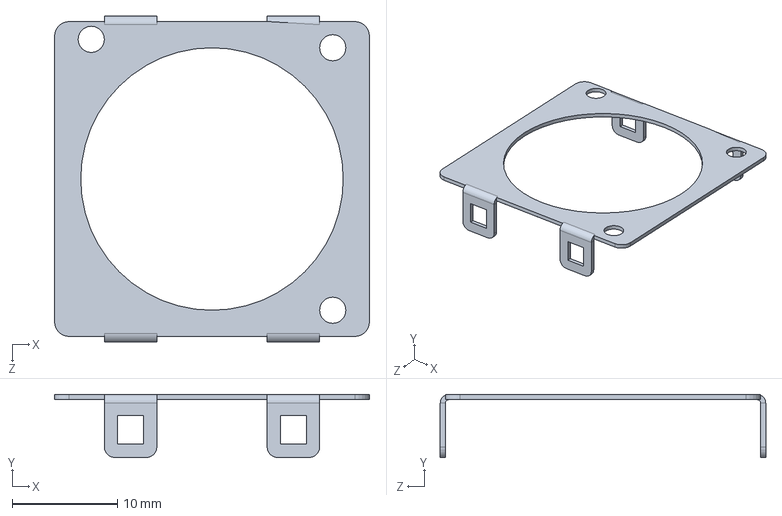
[picture p64: CAD file, 2025-10-28]
Import/RPi Active Cooler/fan cover.SLDPRT
30.0 x 6.00 x 31.0 mm
