Buski10/Offroad-CAD/Import/Silber Kugel.SLDPRT

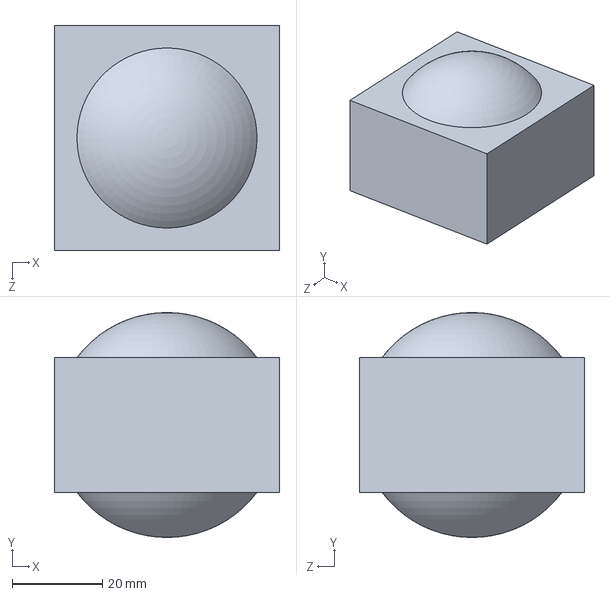
[picture p65: CAD file, 2025-10-28]
Import/Silber Kugel.SLDPRT
50.0 x 50.0 x 50.0 mm
