Buski10/Offroad-CAD/Räder/Gussform rausnehmen.SLDPRT

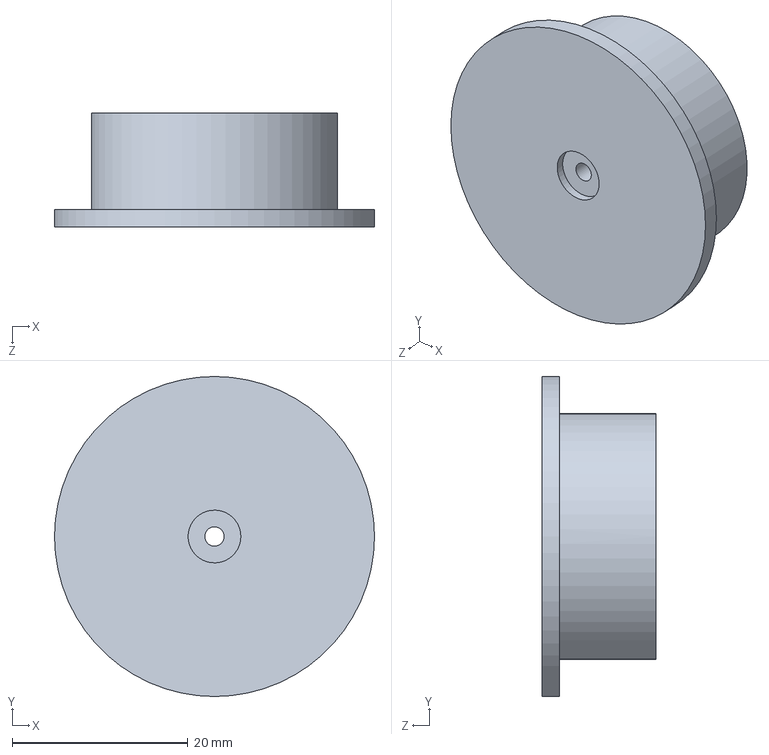
[picture p66: CAD file, 2025-10-28]
Räder/Gussform rausnehmen.SLDPRT
36.4 x 36.4 x 13.0 mm
