Buski10/Offroad-CAD/ToF2 Halterung.SLDPRT

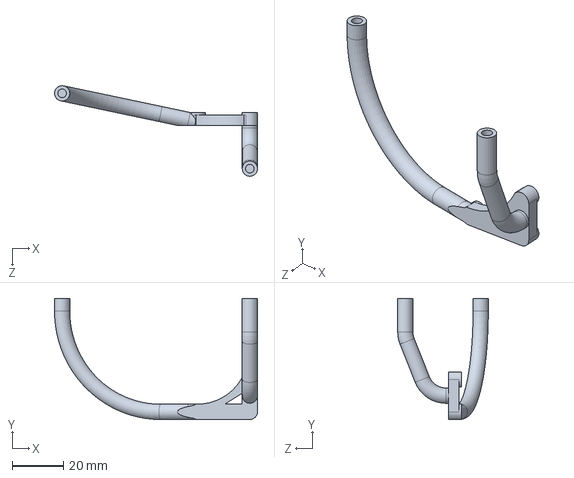
[picture p67: CAD file, 2025-10-28]
ToF2 Halterung.SLDPRT
79.5 x 47.4 x 35.5 mm
