Buski10/Offroad-CAD/Achsenverschluss.SLDPRT

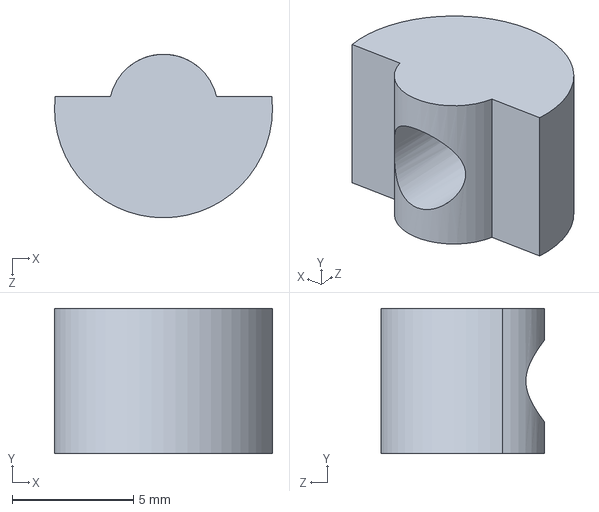
[picture p68: CAD file, 2025-10-28]
Achsenverschluss.SLDPRT
9.00 x 6.00 x 6.75 mm
