Buski10/Offroad-CAD/Import/MOLEX Crimp Stecker.SLDPRT

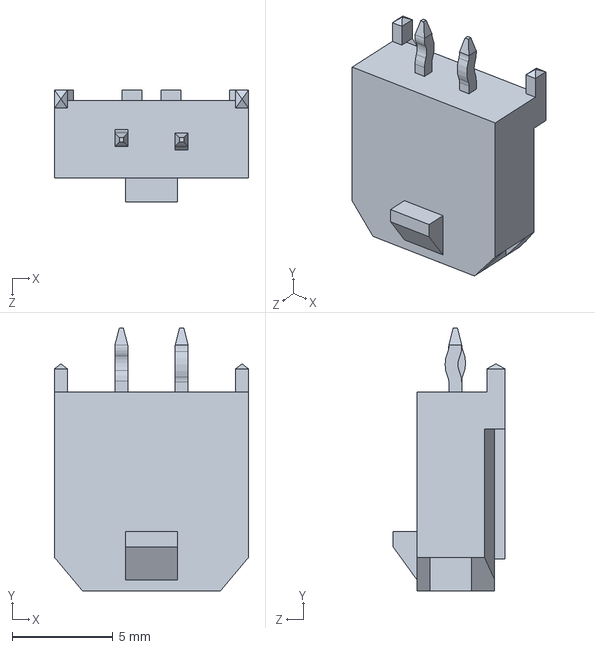
[picture p69: CAD file, 2025-10-28]
Import/MOLEX Crimp Stecker.SLDPRT
9.65 x 13.1 x 5.57 mm
