Buski10/Offroad-CAD/Greifer andere Seite Halterung.SLDPRT

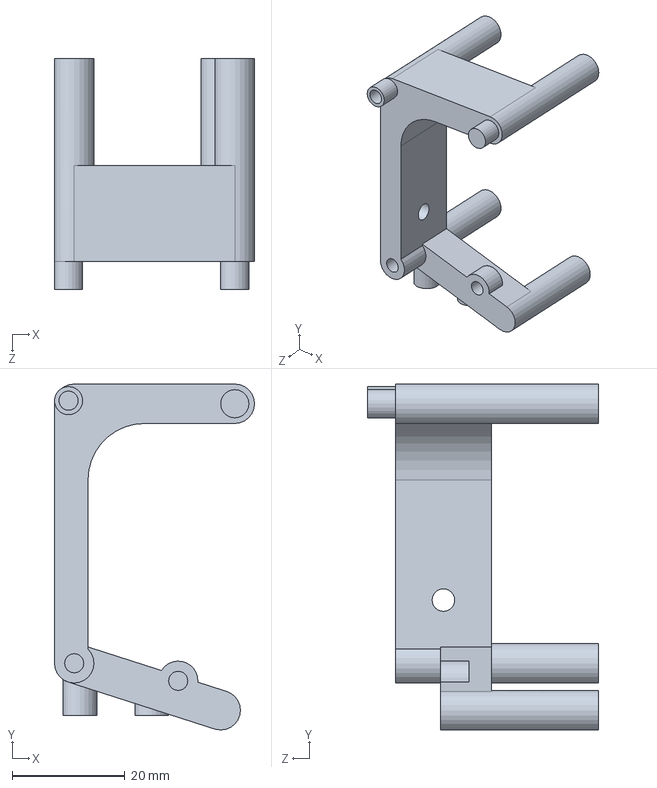
[picture p70: CAD file, 2025-10-28]
Greifer andere Seite Halterung.SLDPRT
35.5 x 61.4 x 41.0 mm
