Buski10/Offroad-CAD/Import/Traco Power TSR 1-2433.SLDPRT

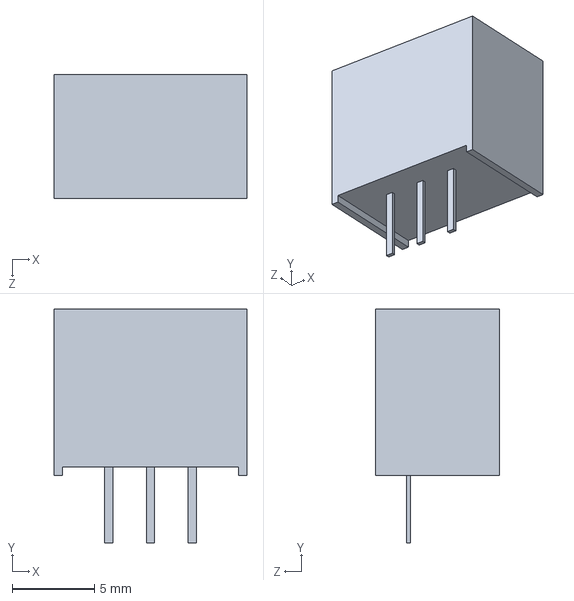
[picture p71: CAD file, 2025-10-28]
Import/Traco Power TSR 1-2433.SLDPRT
11.7 x 14.2 x 7.50 mm
