Buski10/Offroad-CAD/Import/AKL 249-02 Anschlussklemmensystem 2-pol, RM5,08.SLDPRT

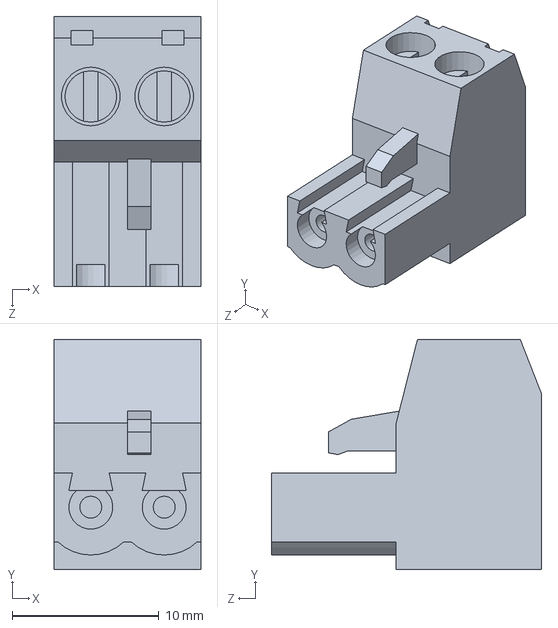
[picture p72: CAD file, 2025-10-28]
Import/AKL 249-02 Anschlussklemmensystem 2-pol, RM5,08.SLDPRT
10.0 x 15.7 x 18.4 mm
