Buski10/Offroad-CAD/Batteriebox.SLDPRT

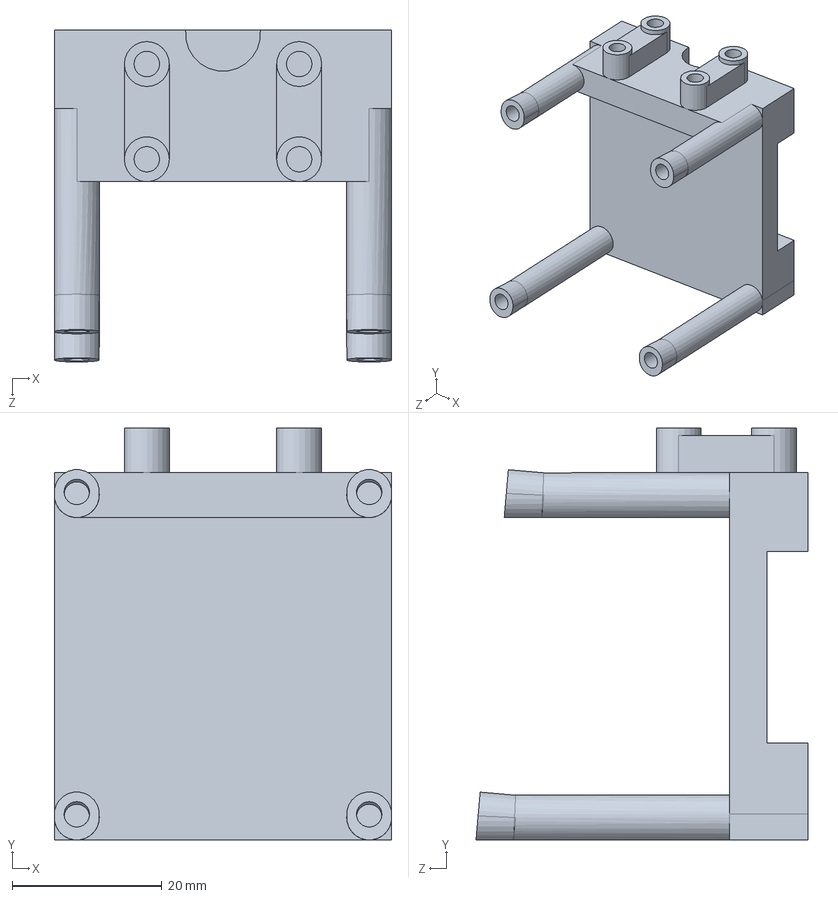
[picture p73: CAD file, 2025-10-28]
Batteriebox.SLDPRT
45.0 x 54.9 x 44.3 mm
