Buski10/Offroad-CAD/Import/JST PH2.0 2.SLDPRT

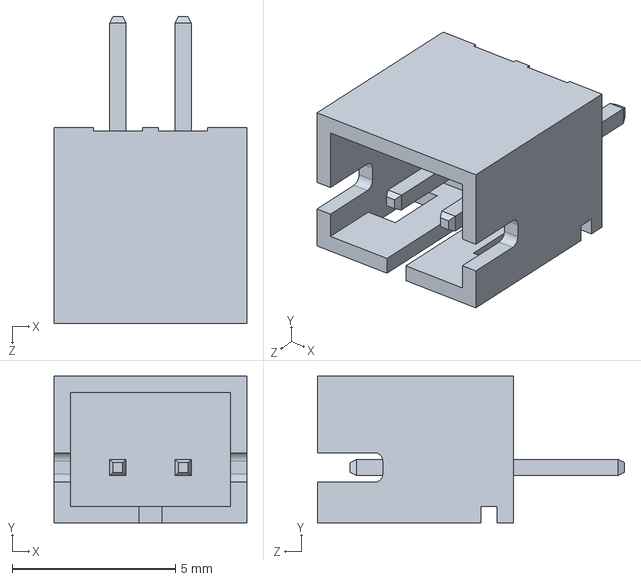
[picture p74: CAD file, 2025-10-28]
Import/JST PH2.0 2.SLDPRT
5.90 x 4.50 x 9.40 mm
