Buski10/Offroad-CAD/Vordere ToF Halterung.SLDPRT

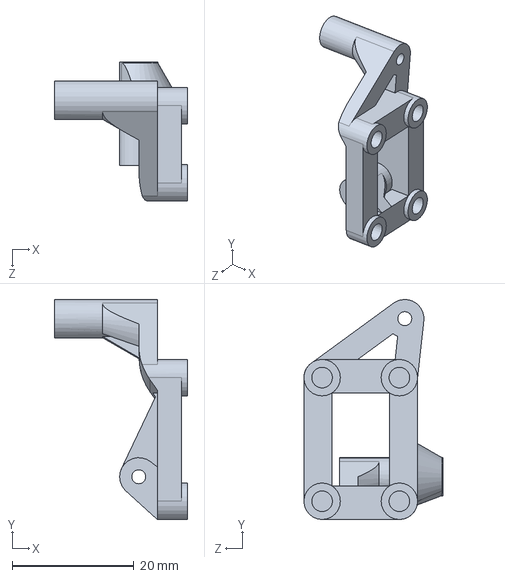
[picture p75: CAD file, 2025-10-28]
Vordere ToF Halterung.SLDPRT
21.9 x 36.2 x 22.9 mm
