Buski10/Offroad-CAD/Import/Tactile Push Button.step.SLDPRT

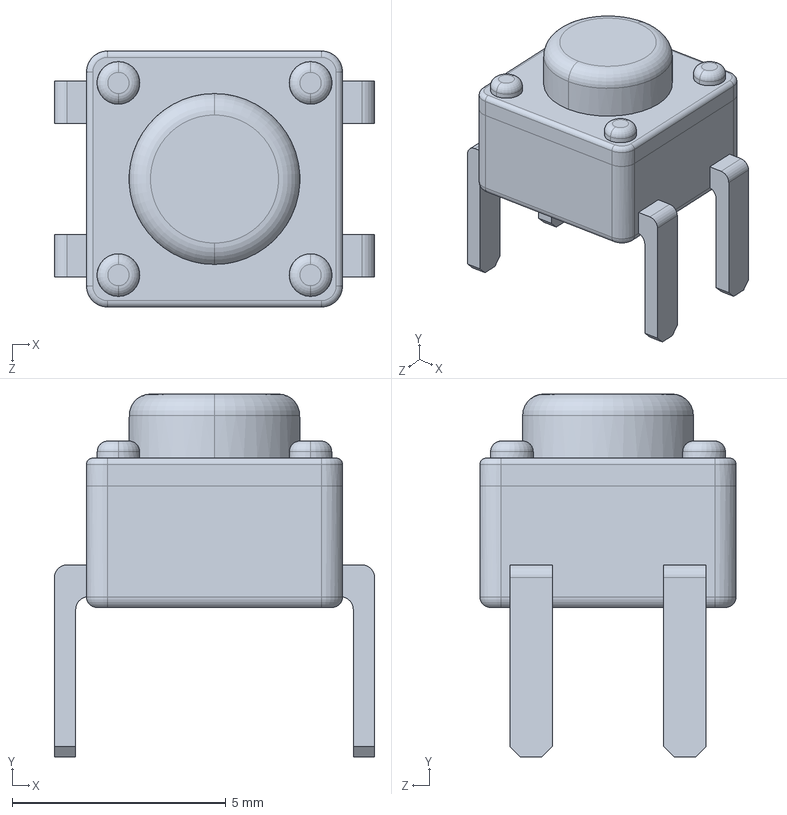
[picture p76: CAD file, 2025-10-28]
Import/Tactile Push Button.step.SLDPRT
7.50 x 8.50 x 6.00 mm
