Buski10/Offroad-CAD/ToF Vorne Rechts Halterung.SLDPRT

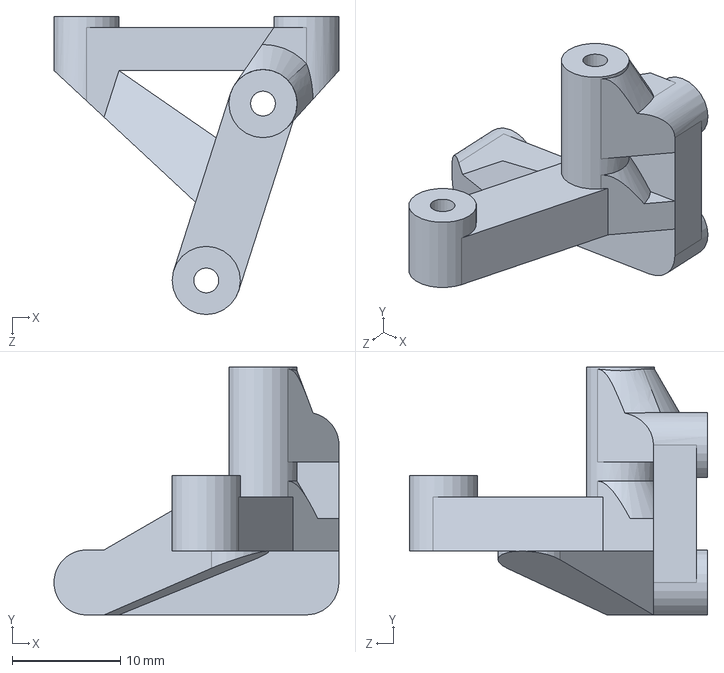
[picture p77: CAD file, 2025-10-28]
ToF Vorne Rechts Halterung.SLDPRT
26.3 x 22.9 x 27.5 mm
