Buski10/Offroad-CAD/Arduino Servo Platinen Halterung.SLDPRT

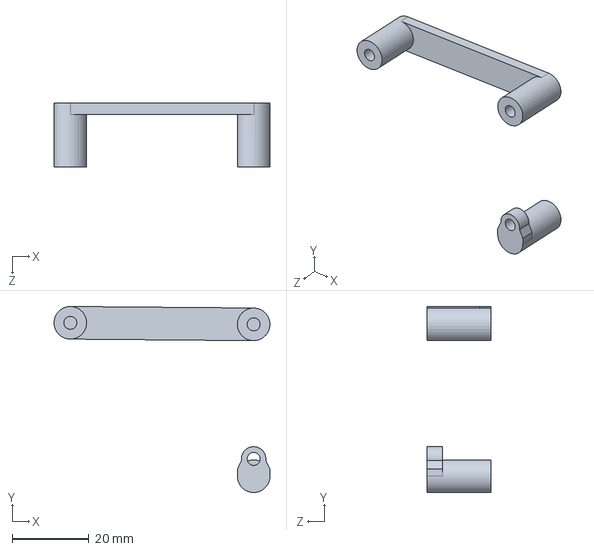
[picture p78: CAD file, 2025-10-28]
Arduino Servo Platinen Halterung.SLDPRT
56.2 x 48.4 x 16.6 mm
