Buski10/Offroad-CAD/Import/LiPo.SLDPRT

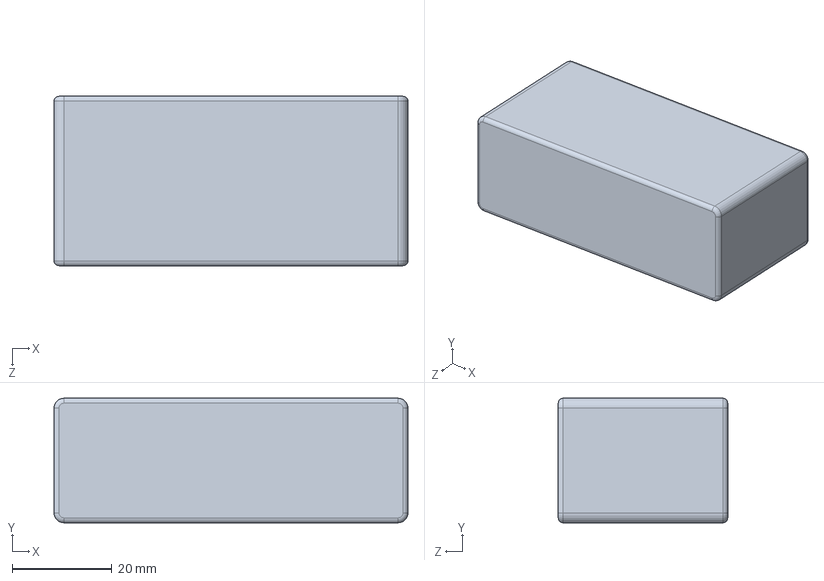
[picture p79: CAD file, 2025-10-28]
Import/LiPo.SLDPRT
71.0 x 25.0 x 34.0 mm
