Buski10/Offroad-CAD/Griff.SLDPRT

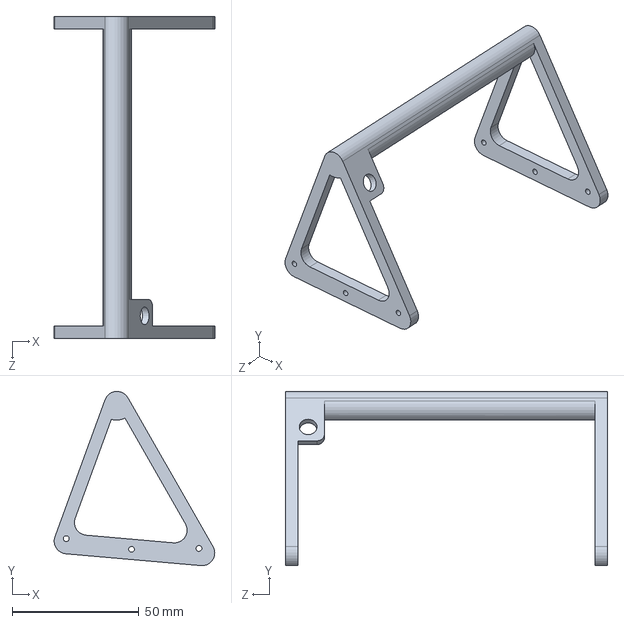
[picture p80: CAD file, 2025-10-28]
Griff.SLDPRT
63.3 x 68.7 x 127.0 mm
