Buski10/Offroad-CAD/Import/5V, 5A step down.SLDPRT

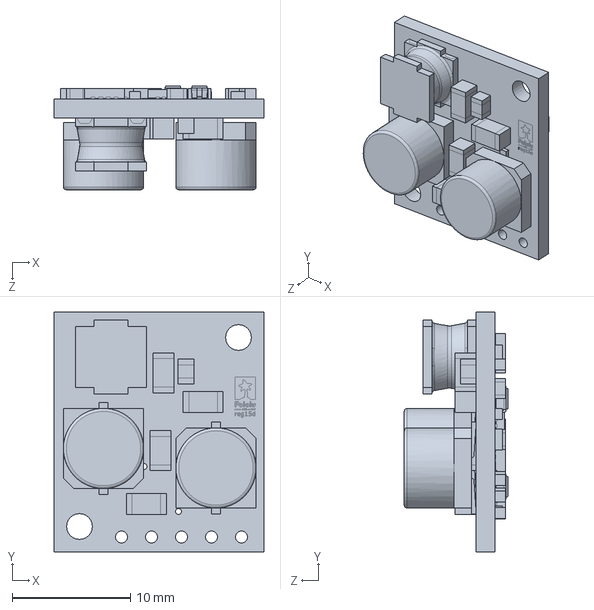
[picture p81: CAD file, 2025-10-28]
Import/5V, 5A step down.SLDPRT
17.8 x 20.3 x 8.77 mm
