Buski10/Offroad-CAD/Import/Servo Platine.SLDPRT

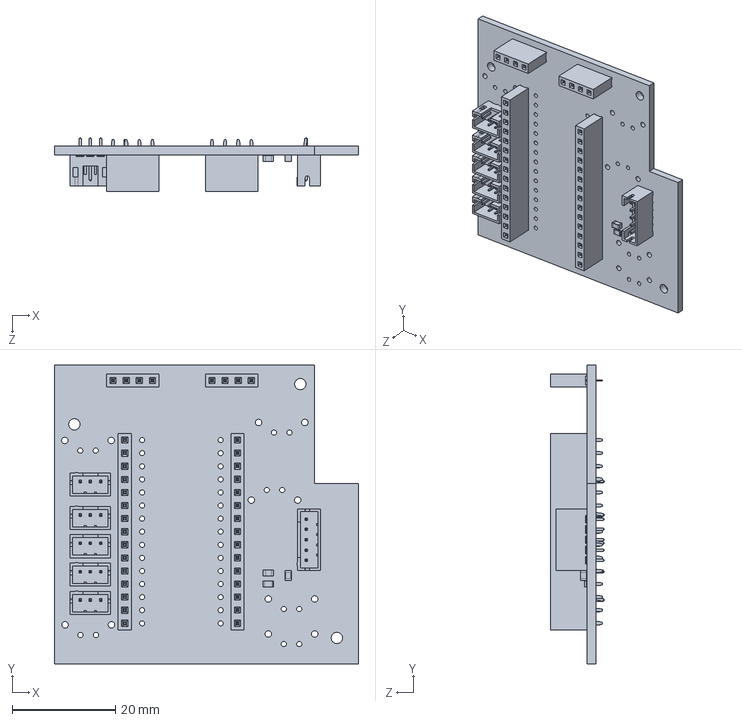
[picture p82: CAD file, 2025-10-28]
Import/Servo Platine.SLDPRT
59.0 x 58.0 x 10.4 mm
