Buski10/Offroad-CAD/Stützen zum testen.SLDPRT

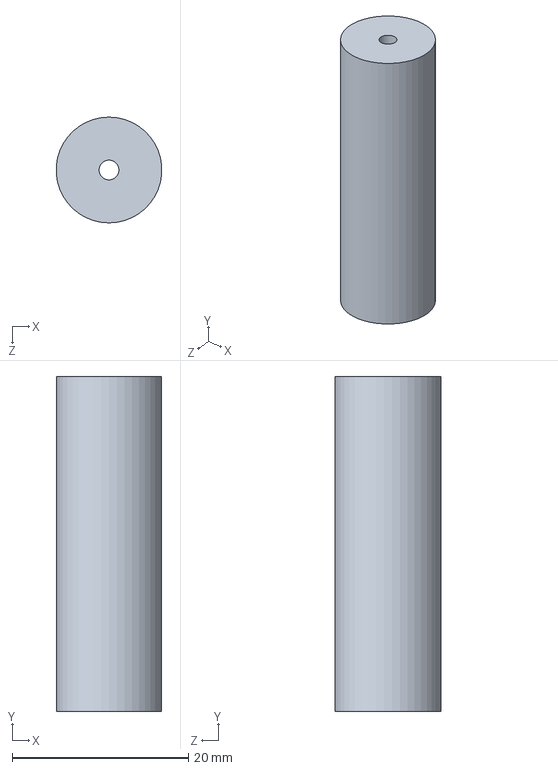
[picture p83: CAD file, 2025-10-28]
Stützen zum testen.SLDPRT
12.0 x 38.0 x 12.0 mm
