Buski10/Offroad-CAD/Import/MG90S horn.SLDPRT

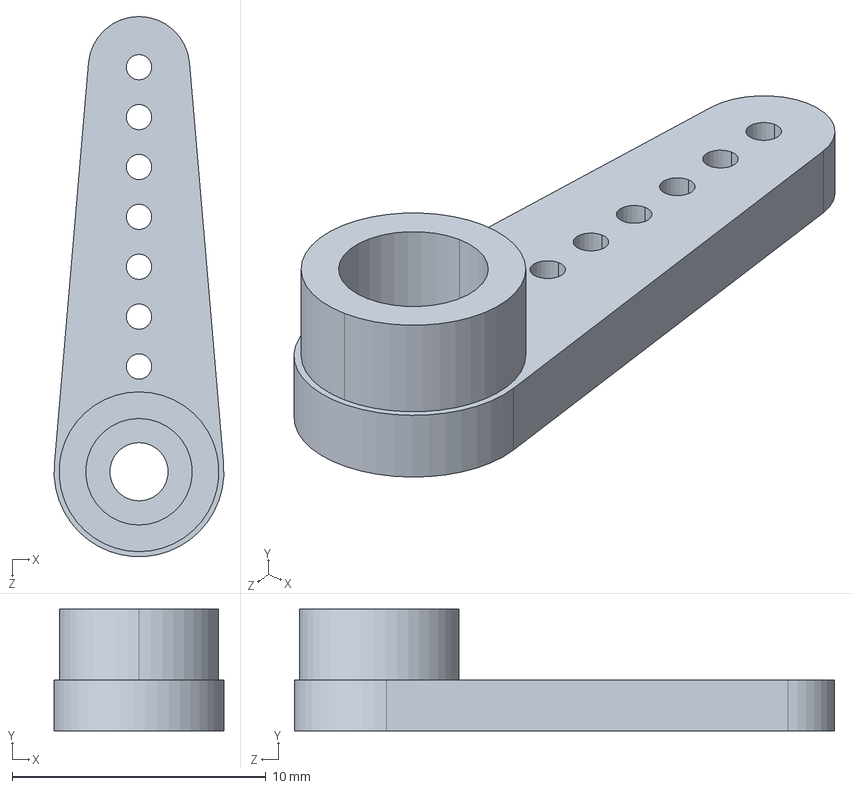
[picture p84: CAD file, 2025-10-28]
Import/MG90S horn.SLDPRT
6.69 x 4.80 x 21.3 mm
