Buski10/Offroad-CAD/Spannungswandlerhalterung.SLDPRT

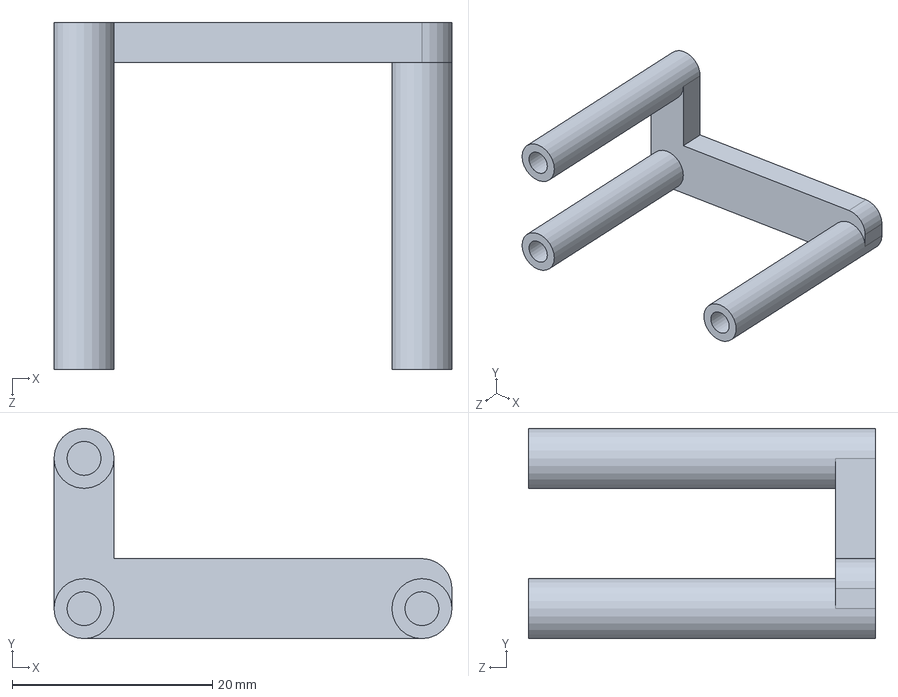
[picture p85: CAD file, 2025-10-28]
Spannungswandlerhalterung.SLDPRT
39.7 x 21.0 x 34.6 mm
