Buski10/Offroad-CAD/Import/Distanzbolzen M3.SLDPRT

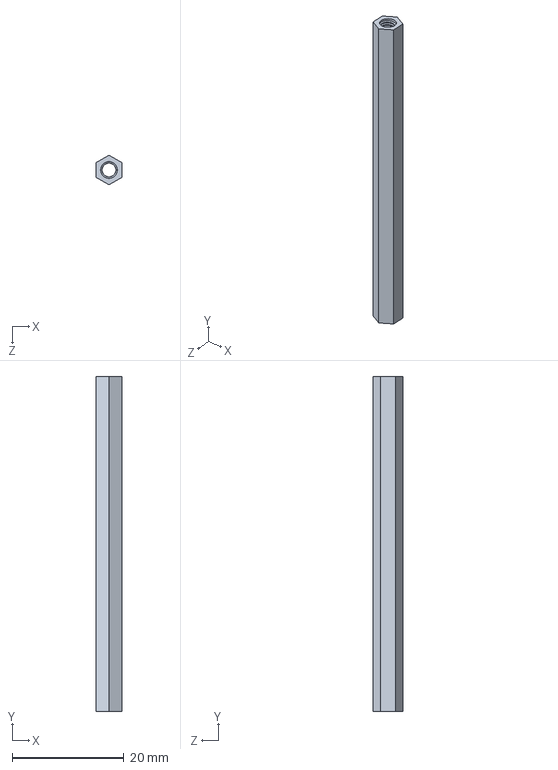
[picture p86: CAD file, 2025-10-28]
Import/Distanzbolzen M3.SLDPRT
4.60 x 60.0 x 5.31 mm
