Buski10/Offroad-CAD/Import/VL53L0X TOF Sensor.SLDPRT

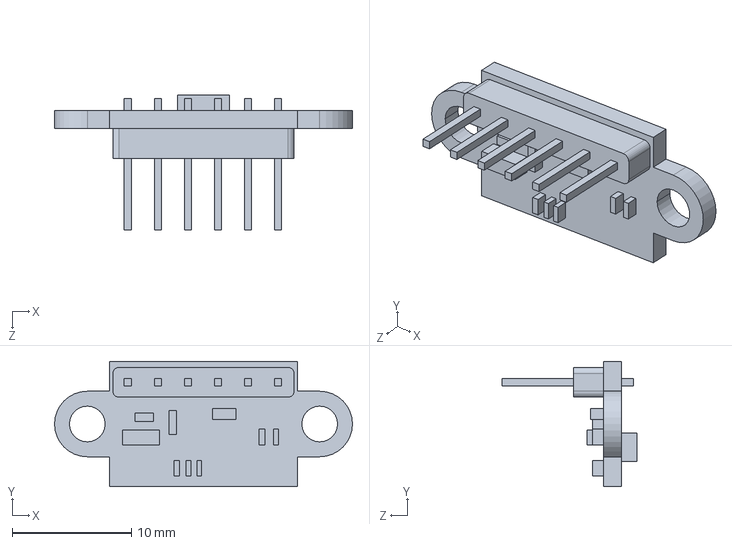
[picture p87: CAD file, 2025-10-28]
Import/VL53L0X TOF Sensor.SLDPRT
25.0 x 10.5 x 11.3 mm
