Buski10/Offroad-CAD/Import/Info LEDS.SLDPRT

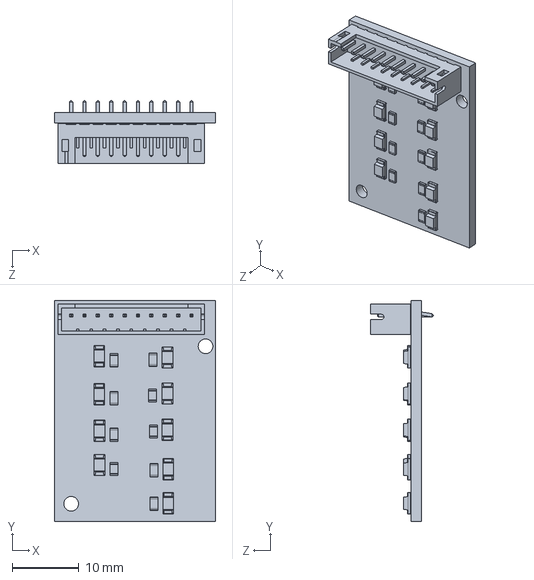
[picture p88: CAD file, 2025-10-28]
Import/Info LEDS.SLDPRT
24.1 x 33.0 x 9.40 mm
