Buski10/Offroad-CAD/Import/Gewicht.SLDPRT

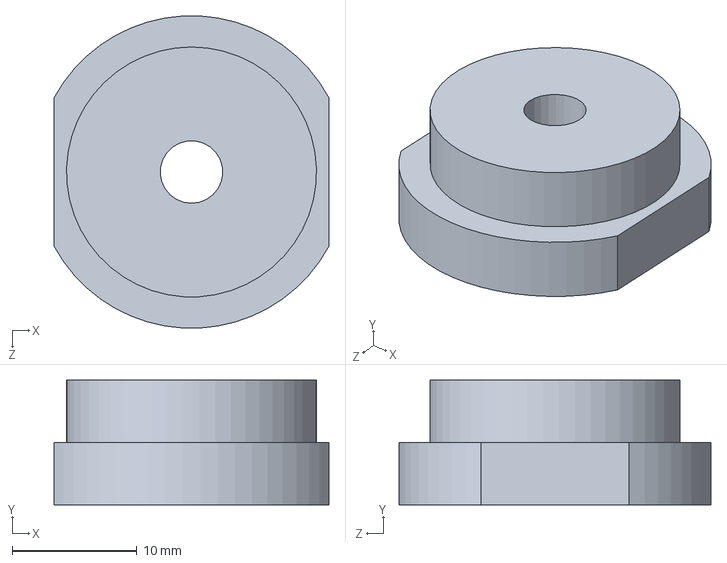
[picture p89: CAD file, 2025-10-28]
Import/Gewicht.SLDPRT
22.0 x 10.0 x 25.0 mm
