Buski10/Offroad-CAD/Import/Distanzbolzen M3 12mm.SLDPRT

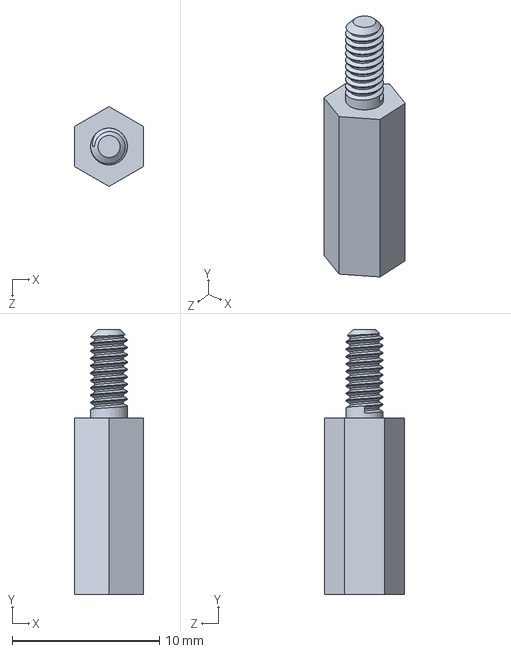
[picture p90: CAD file, 2025-10-28]
Import/Distanzbolzen M3 12mm.SLDPRT
4.70 x 18.0 x 5.43 mm
