Buski10/Offroad-CAD/Import/AKL 230-02 Wannenstecker für AKL 249, 2-pol, RM5,08.SLDPRT

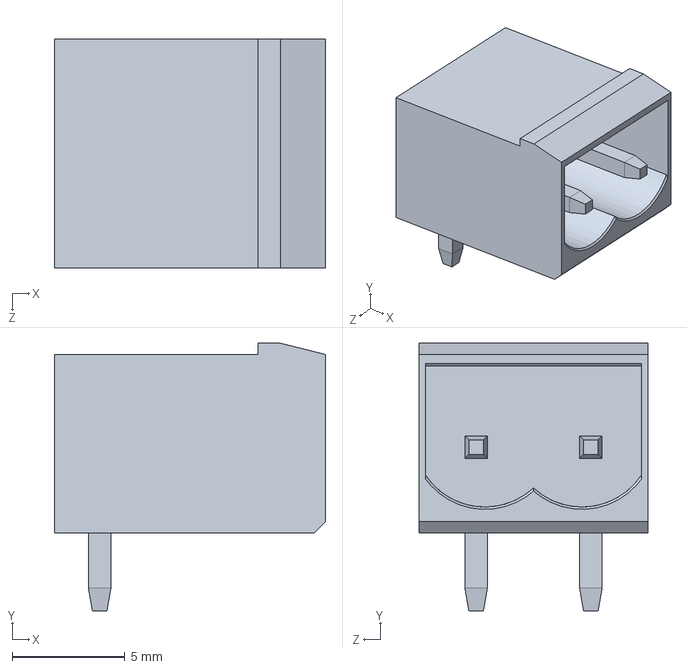
[picture p91: CAD file, 2025-10-28]
Import/AKL 230-02 Wannenstecker für AKL 249, 2-pol, RM5,08.SLDPRT
12.0 x 11.8 x 10.2 mm
