Buski10/Offroad-CAD/Import/Gyro Platine rechts.SLDASM

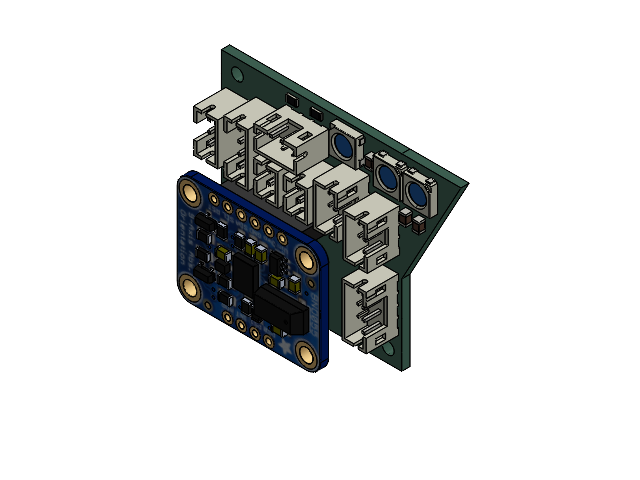
[picture p96: CAD file, 2025-10-28]
Import/Gyro Platine rechts.SLDASM
JST_B4B_PH_K.step x 2
PinSocket_1x06_P254mm_Vertical.step
JST_B3B_PH_K.step x 4
R_0805_2012Metric-0.step x 3
PinSocket_1x04_P254mm_Vertical.step
C_0805_2012Metric-0.step x 3
LED_WS2812B_PLCC4_50x50mm_P32mm.step x 3
JST_B2B_PH_K.step x 2
Gyro Platine_PCB.step
Adafruit_BNO055
