Buski10/Offroad-CAD/Import/LED Ring.SLDASM

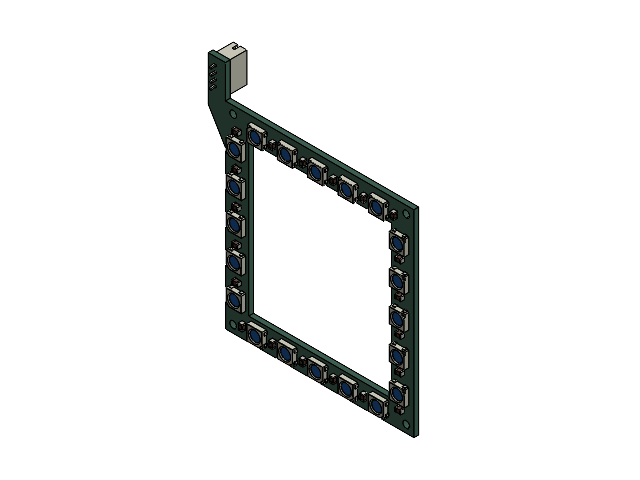
[picture p97: CAD file, 2025-10-28]
Import/LED Ring.SLDASM
C_0805_2012Metric-0.step x 20
LED_WS2812B_PLCC4_50x50mm_P32mm.step x 20
JST_B4B_PH_K.step
LED Ring_PCB.step
