Buski10/Offroad-CAD/Import/Stromverteiler.SLDASM

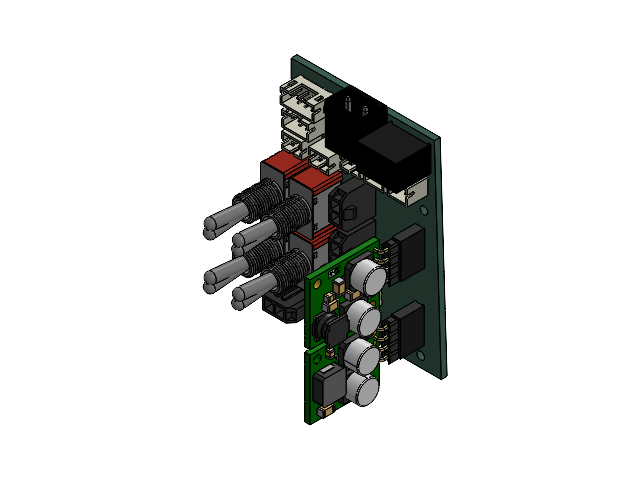
[picture p98: CAD file, 2025-10-28]
Import/Stromverteiler.SLDASM
JST_B4B_PH_K_1.step x 2
R_0805_2012Metric-0_1.step x 4
JST_B2B_PH_K_1.step x 6
JST_B3B_PH_K_1.step x 2
SOT_23_1.step
PinSocket_1x04_P254mm_Vertical_1.step x 2
Stromverteiler Platine mit TOF 19.07.24_PCB_1.step
AKL 230-02 Wannenstecker für AKL 249, 2-pol, RM5,08
1x4 Male Pin Header Angle x 2
5V, 5A step down
7.5V, 3A step down
Hebel.step x 8
MOLEX Crimp Stecker x 4
Traco Power TSR 1-2433
