Buski10/Offroad-CAD/Import/Gyro Platine links.SLDASM

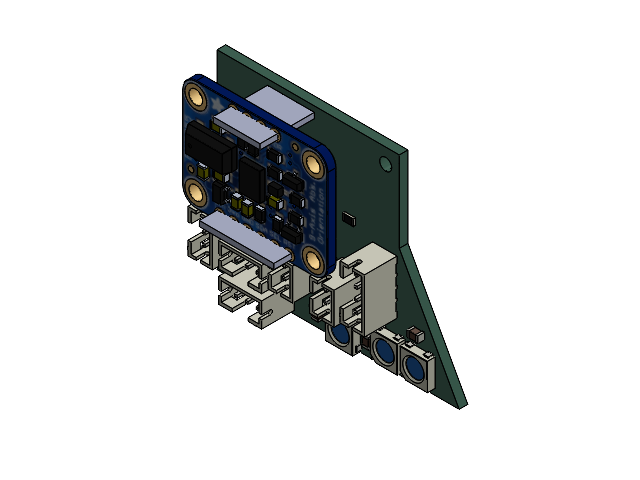
[picture p99: CAD file, 2025-10-28]
Import/Gyro Platine links.SLDASM
JST_B4B_PH_K_1.step
JST_B2B_PH_K_1.step x 2
LED_WS2812B_PLCC4_50x50mm_P32mm_1.step x 3
JST_B3B_PH_K_1.step x 3
C_0805_2012Metric-0.step x 3
R_0805_2012Metric-0_1.step x 3
Gyro Platine links_PCB.step
Big Shit Gyro 2
Adafruit_BNO055
