Buski10/Offroad-CAD/Import/Knöpfe platine.SLDASM

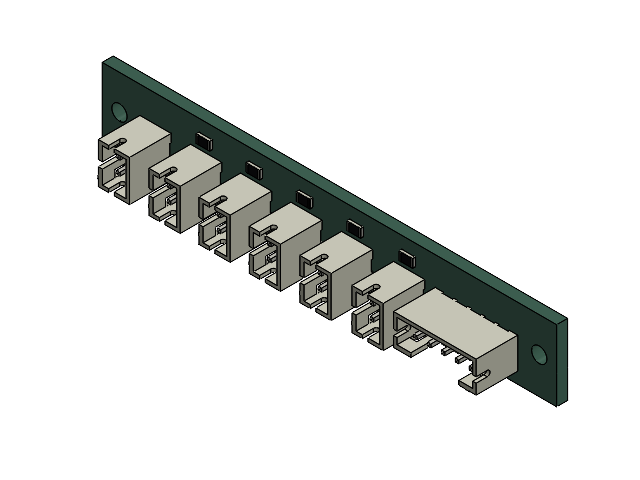
[picture p100: CAD file, 2025-10-28]
Import/Knöpfe platine.SLDASM
JST_B2B_PH_K.step x 6
JST_B5B_PH_K_1.step
R_0805_2012Metric-0.step x 5
Kn____pfe platine_PCB.step
